DAlexis/caustic-lasertag-system/schematic/bridge/bridge-iron-rev1/bridge-iron-rev1.kicad_pcb

## KiCad design schematic/bridge/bridge-iron-rev1/bridge-iron-rev1.kicad_pcb (2015-09-06)

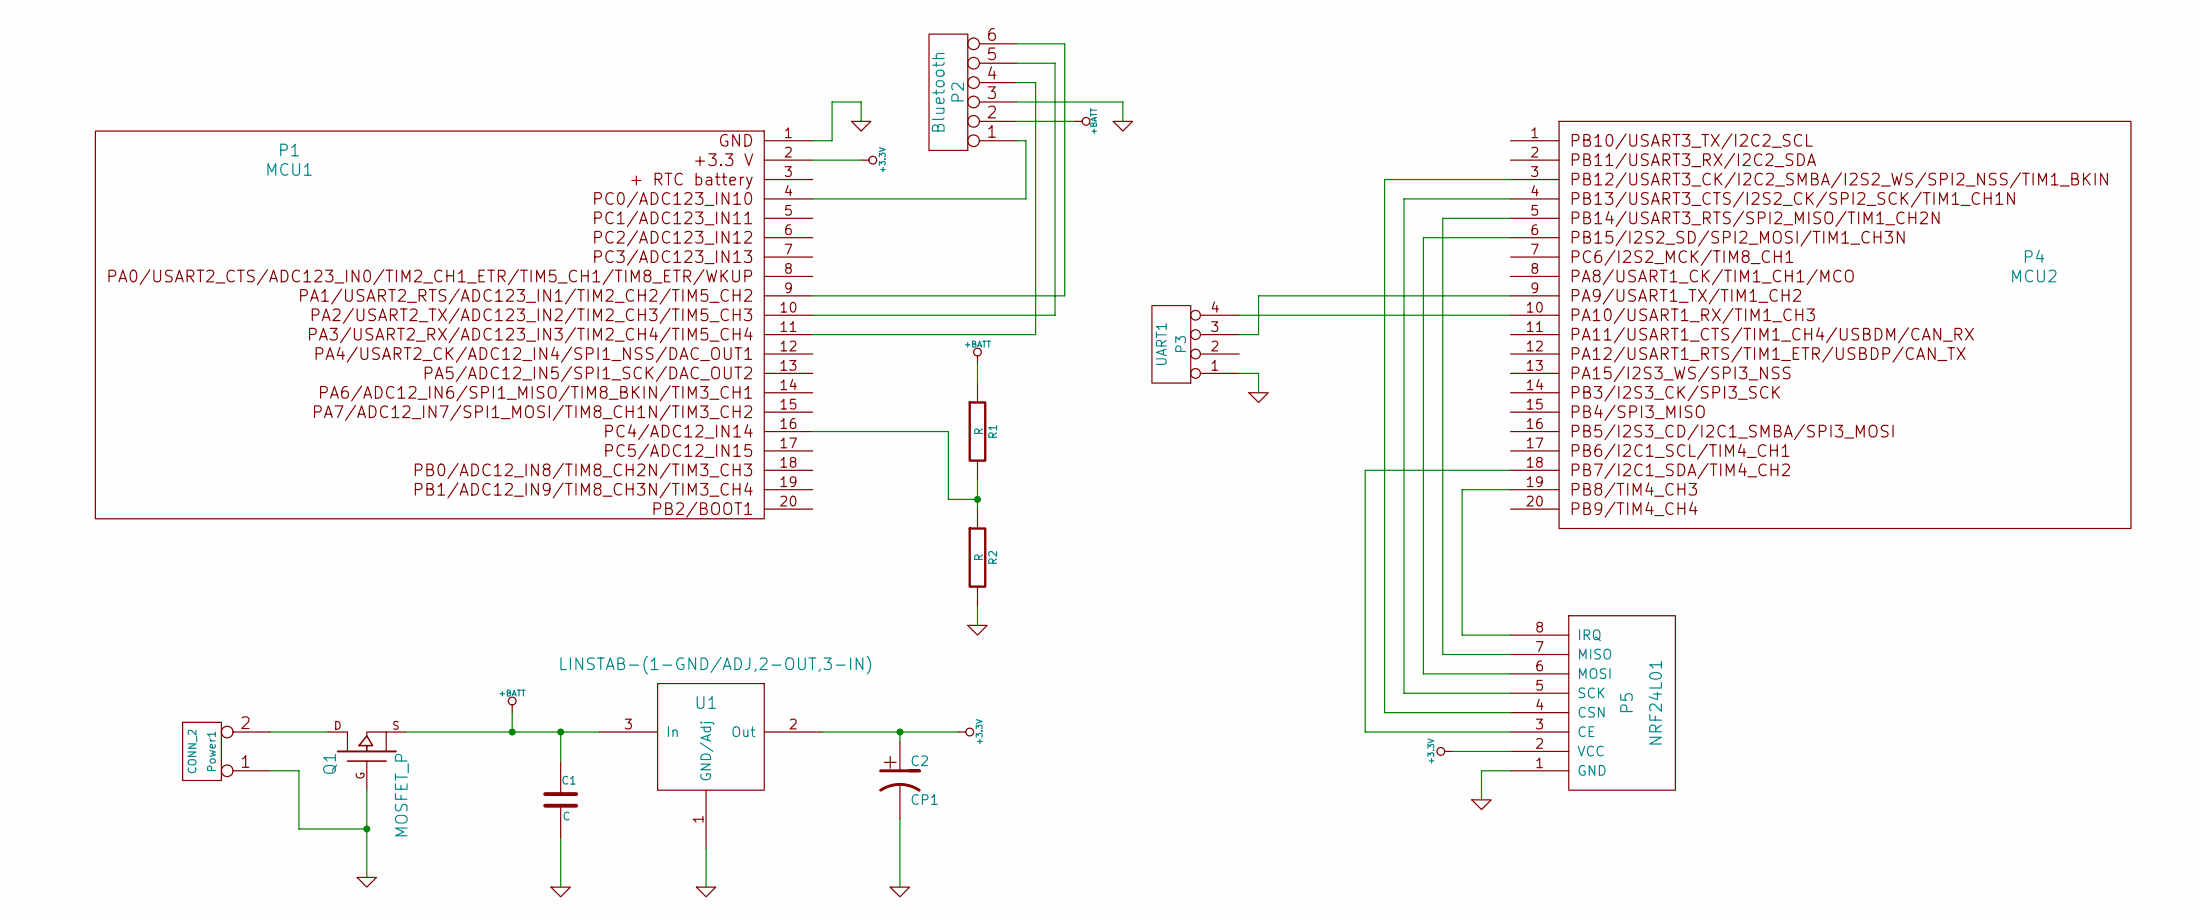
[picture p26: schematic bridge-iron-rev1.sch]

Parts:
C1: C
C2: CP1
P1: MCU1
P2: Bluetooth
P3: UART1
P4: MCU2
P5: NRF24L01
Power1: CONN_2
Q1: MOSFET_P
R1, R2: R
U1: LINSTAB-(1-GND/ADJ,2-OUT,3-IN)

Connections:
+3.3V: C2.1, P1.2, P5.2 (VCC), U1.2 (Out)
+BATT: C1.1, P2.2, Q1.S, R1.1, U1.3 (In)
GND: C1.2, C2.2, P1.1, P2.3, P3.1, P5.1 (GND), Power1.1, Q1.G, R2.2, U1.1 (GND/Adj)
unnamed: P4.18, P5.3 (CE)
unnamed: P3.3, P4.9
unnamed: P3.4, P4.10
unnamed: P4.4, P5.5 (SCK)
unnamed: P4.6, P5.6 (MOSI)
unnamed: P4.5, P5.7 (MISO)
unnamed: P4.19, P5.8 (IRQ)
unnamed: P4.3, P5.4 (CSN)
unnamed: P1.9, P2.6
unnamed: P1.4, P2.1
unnamed: Power1.2 (PM), Q1.D
unnamed: P1.11, P2.4
unnamed: P1.10, P2.5
unnamed: P1.16, R1.2, R2.1

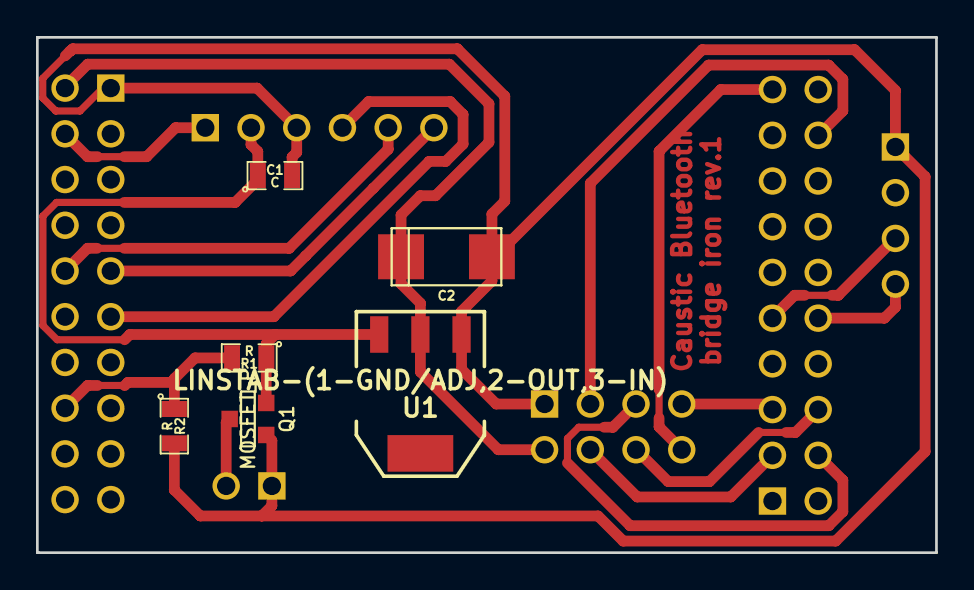
[picture p27: board bridge-iron-rev1.kicad_pcb from above]

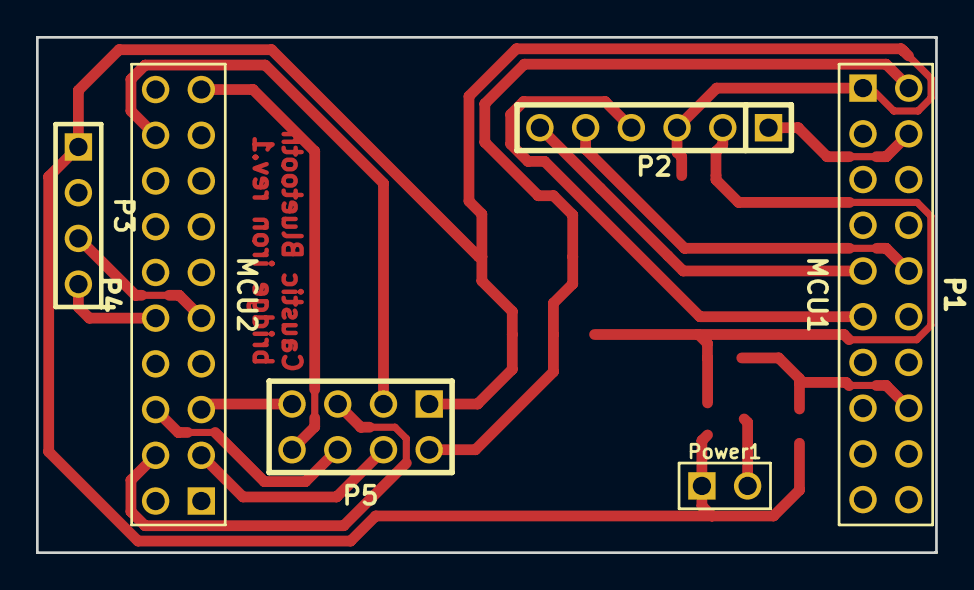
[picture p28: board bridge-iron-rev1.kicad_pcb from below]

Board: 2 copper layers, 50.0 x 28.6 mm, 12 parts (6 on the bottom side), 17 nets.
