DAlexis/caustic-lasertag-system/schematic/head-sensor/head-sensor-shield-v1-rev1/head-sensor-shield-v1-rev1.kicad_pcb

## KiCad design schematic/head-sensor/head-sensor-shield-v1-rev1/head-sensor-shield-v1-rev1.kicad_pcb (2015-08-30, an earlier design)

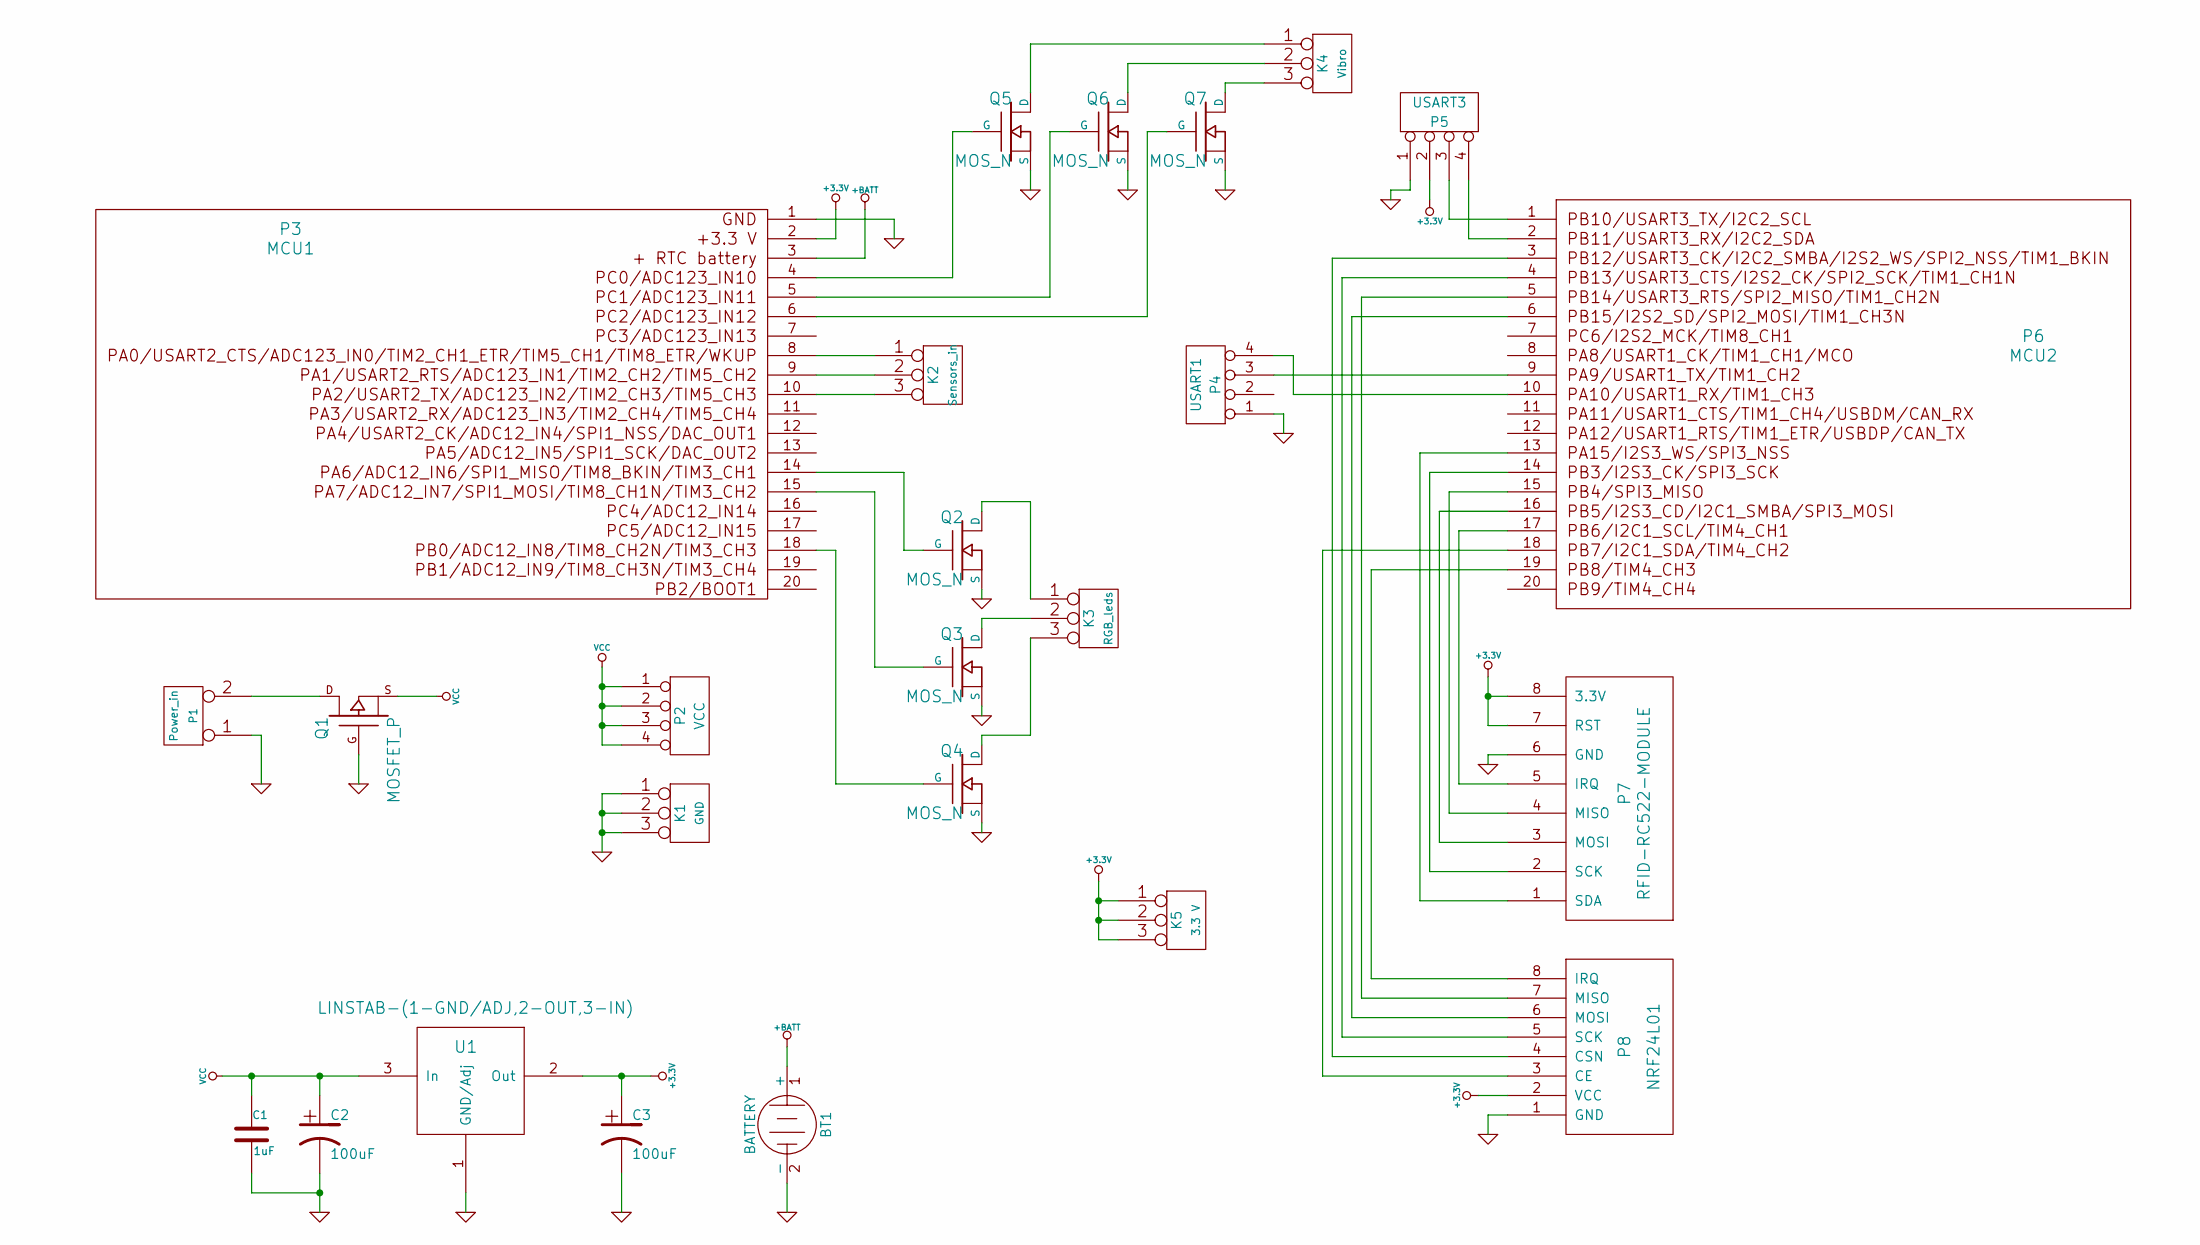
[picture p29: schematic head-sensor-shield-v1-rev1.sch]

Parts:
BT1: BATTERY
C1: 1uF
C2, C3: 100uF
K1: GND
K2: Sensors_in
K3: RGB_leds
K4: Vibro
K5: 3.3 V
P1: Power_in
P2: VCC
P3: MCU1
P4: USART1
P5: USART3
P6: MCU2
P7: RFID-RC522-MODULE
P8: NRF24L01
Q1: MOSFET_P
Q2, Q3, Q4, Q5, Q6, Q7: MOS_N
U1: LINSTAB-(1-GND/ADJ,2-OUT,3-IN)

Connections:
+3.3V: C3.1, K5.1, K5.2 (PM), K5.3, P3.2, P5.2, P7.7 (RST), P7.8 (3.3V), P8.2 (VCC), U1.2 (Out)
+BATT: BT1.1 (+), P3.3
GND: BT1.2 (-), C1.2, C2.2, C3.2, K1.1, K1.2 (PM), K1.3, P1.1, P3.1, P4.1, P5.1, P7.6 (GND), P8.1 (GND), Q1.G, Q2.S, Q3.S, Q4.S, Q5.S, Q6.S, Q7.S, U1.1 (GND/Adj)
unnamed: P3.6, Q7.G
unnamed: K4.2 (PM), Q6.D
unnamed: K4.3, Q7.D
unnamed: K4.1, Q5.D
unnamed: P3.5, Q6.G
unnamed: P3.4, Q5.G
unnamed: P3.18, Q4.G
unnamed: P3.15, Q3.G
unnamed: K2.1, P3.8
unnamed: K2.3, P3.10
unnamed: K2.2 (PM), P3.9
unnamed: P5.4, P6.2
unnamed: P5.3, P6.1
unnamed: P1.2 (PM), Q1.D
unnamed: P3.14, Q2.G
unnamed: K3.2 (PM), Q3.D
unnamed: K3.3, Q4.D
unnamed: K3.1, Q2.D
unnamed: P6.17, P7.5 (IRQ)
unnamed: P6.13, P7.1 (SDA)
unnamed: P6.14, P7.2 (SCK)
unnamed: P6.16, P7.3 (MOSI)
unnamed: P6.15, P7.4 (MISO)
unnamed: P6.19, P8.8 (IRQ)
unnamed: P6.18, P8.3 (CE)
unnamed: P6.6, P8.6 (MOSI)
unnamed: P6.5, P8.7 (MISO)
unnamed: P6.4, P8.5 (SCK)
unnamed: P6.3, P8.4 (CSN)
unnamed: P4.3, P6.9
unnamed: P4.4, P6.10
VCC: C1.1, C2.1, P2.1, P2.2, P2.3, P2.4, Q1.S, U1.3 (In)

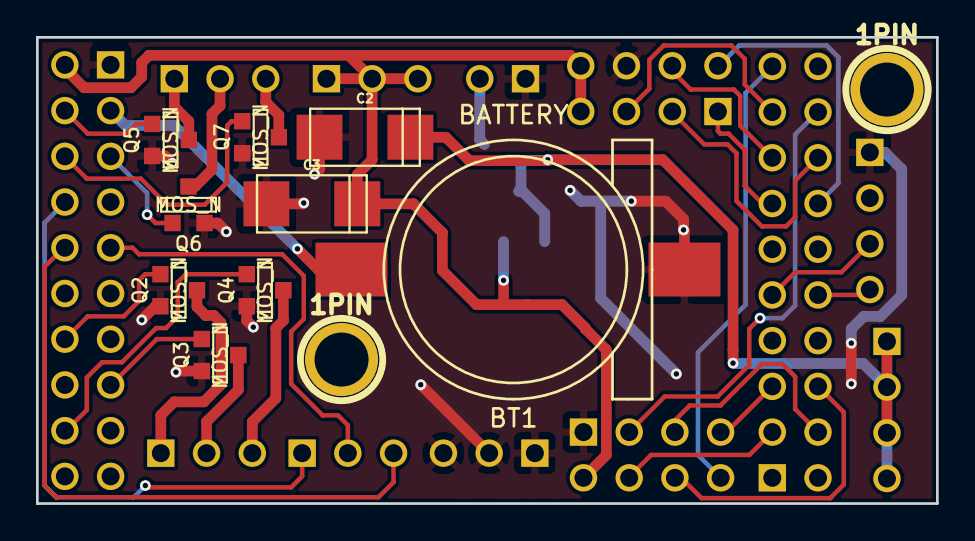
[picture p30: board head-sensor-shield-v1-rev1.kicad_pcb from above]

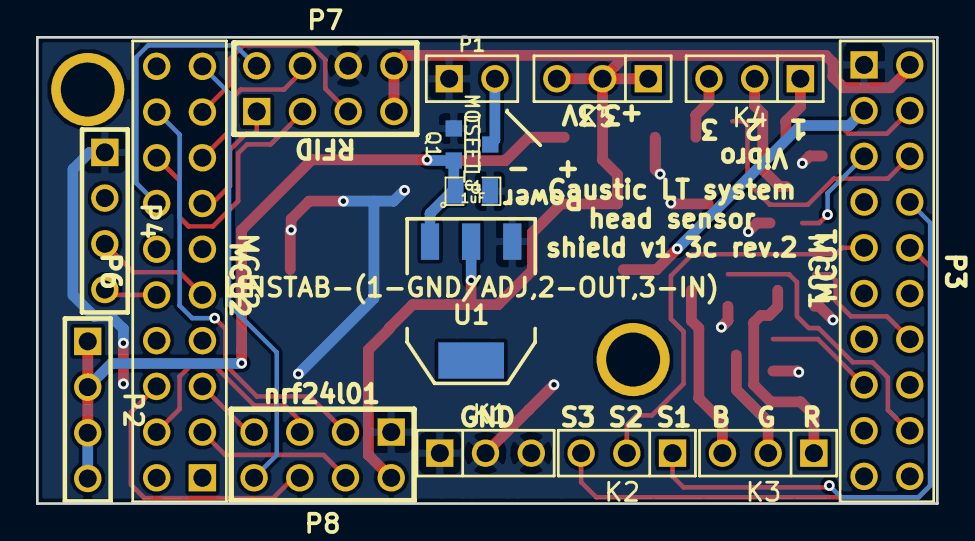
[picture p31: board head-sensor-shield-v1-rev1.kicad_pcb from below]

Board: 2 copper layers, 50.0 x 25.9 mm, 26 parts (15 on the bottom side), 33 nets.

Other parts of the board:
1PIN, 1PIN#2: P***; 1pin
