DAlexis/caustic-lasertag-system/schematic/rifle/rifle-shield-v1-rev1/rifle-shield-v1.kicad_pcb

## KiCad design schematic/rifle/rifle-shield-v1-rev1/rifle-shield-v1.kicad_pcb (2015-07-31)

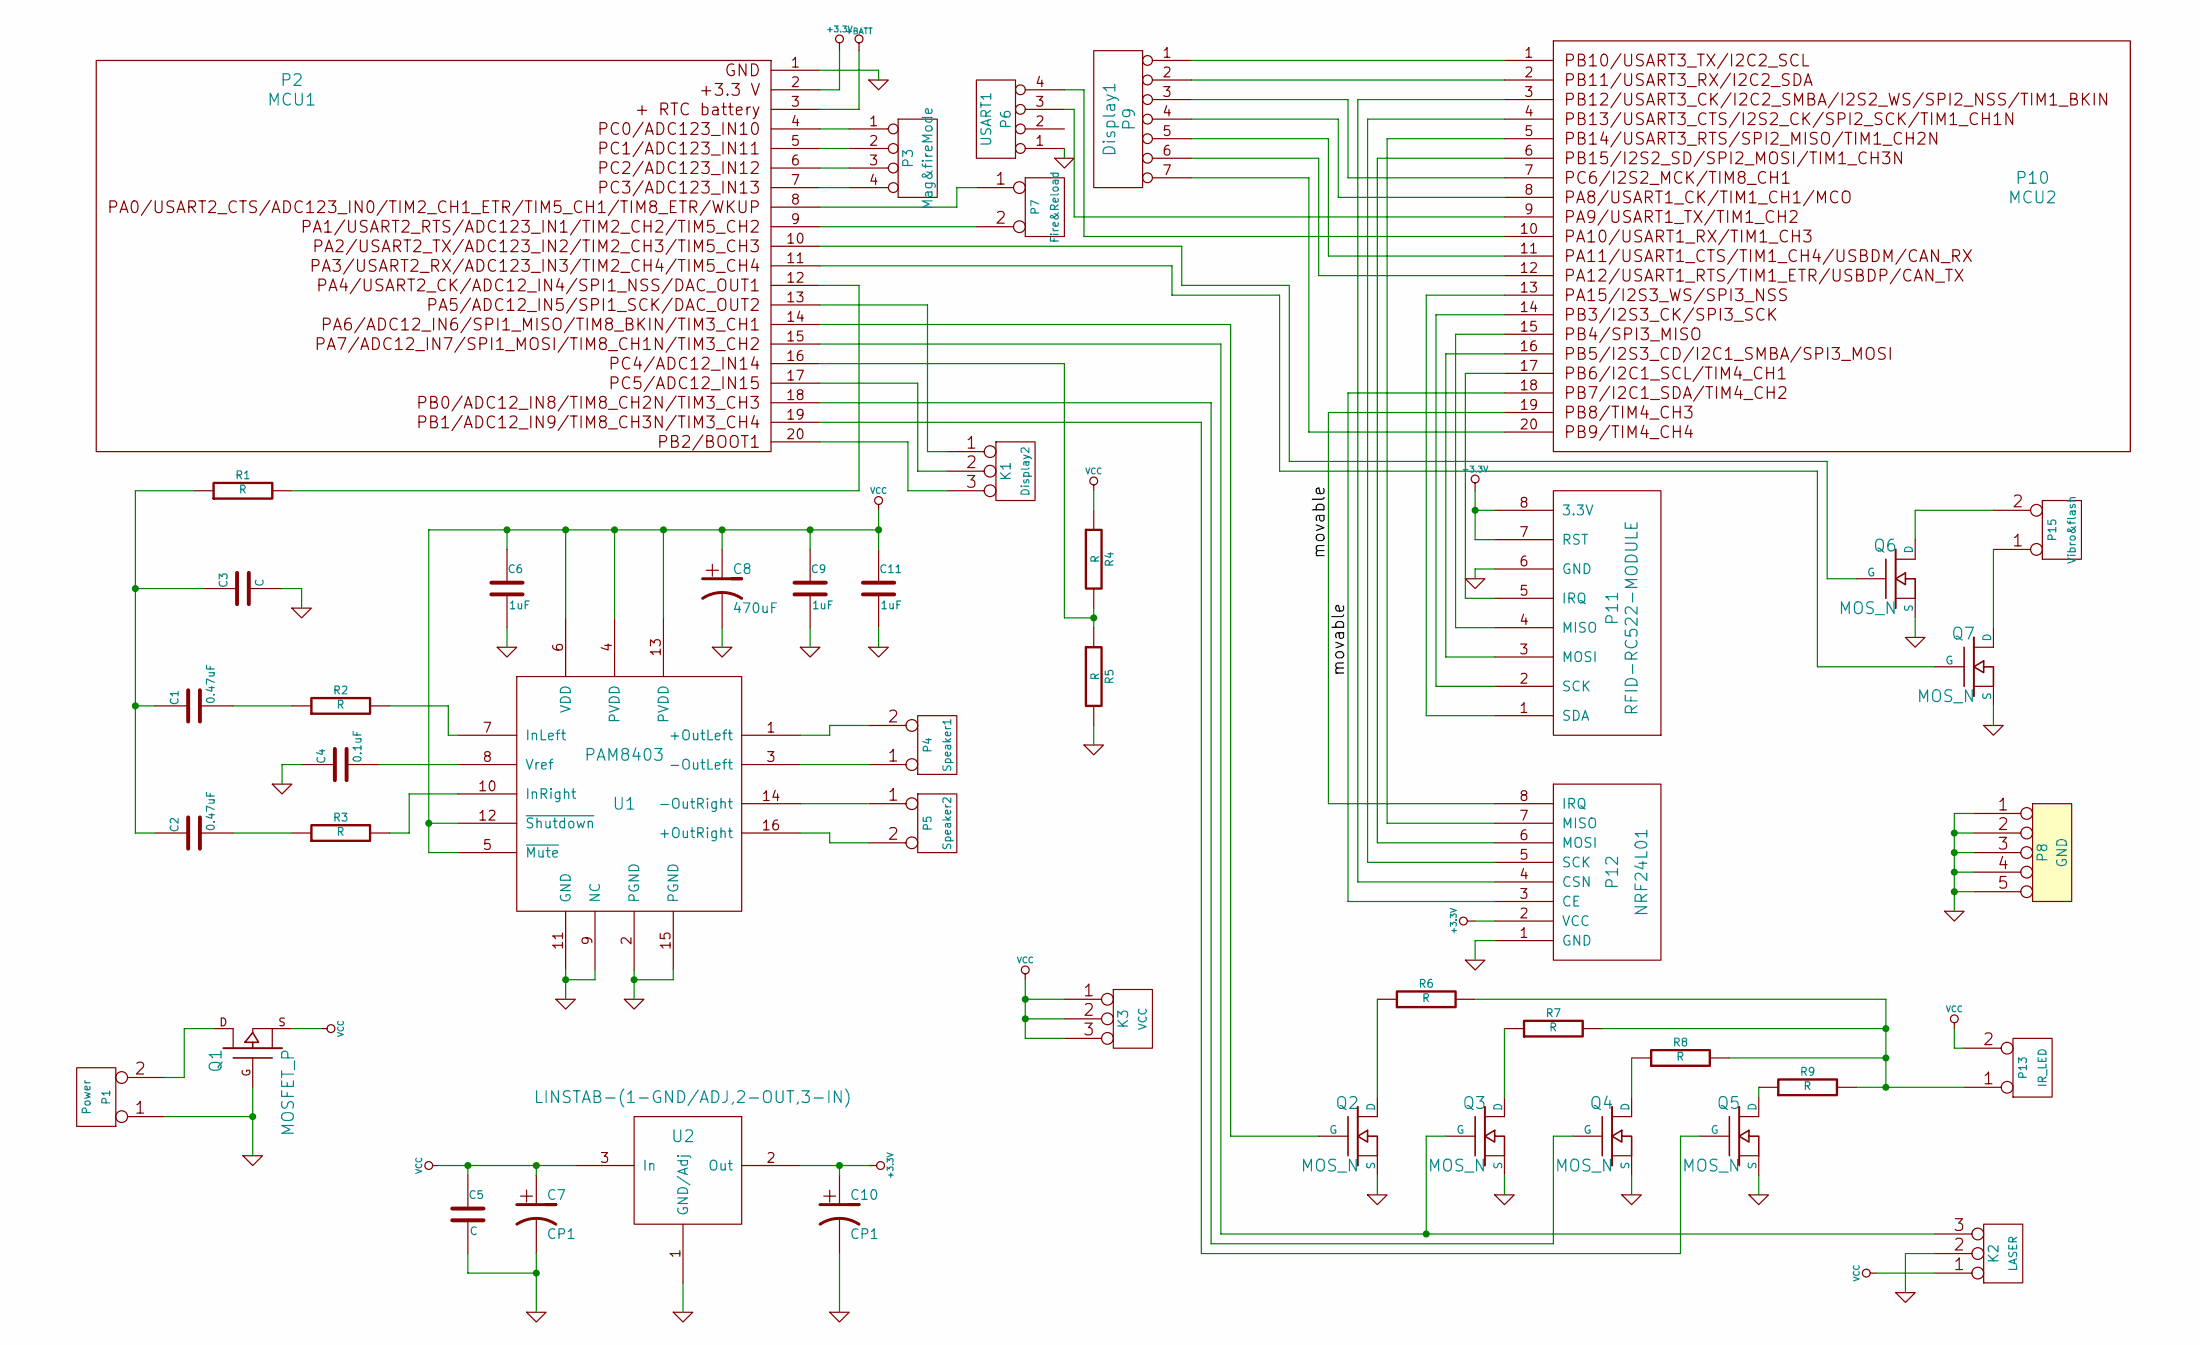
[picture p32: schematic rifle-shield-v1.sch]

Parts:
C1, C2: 0.47uF
C3, C5: C
C4: 0.1uF
C6, C9, C11: 1uF
C7, C10: CP1
C8: 470uF
K1: Display2
K2: LASER
K3: VCC
P1: Power
P2: MCU1
P3: Mag&fireMode
P4: Speaker1
P5: Speaker2
P6: USART1
P7: Fire&Reload
P8: GND
P9: Display1
P10: MCU2
P11: RFID-RC522-MODULE
P12: NRF24L01
P13: IR_LED
P15: Vibro&flash
Q1: MOSFET_P
Q2, Q3, Q4, Q5, Q6, Q7: MOS_N
R1, R2, R3, R4, R5, R6, R7, R8, R9: R
U1: PAM8403
U2: LINSTAB-(1-GND/ADJ,2-OUT,3-IN)

Connections:
+3.3V: C10.1, P2.2, P11.7 (RST), P11.8 (3.3V), P12.2 (VCC), U2.2 (Out)
/movable: P10.18, P10.19, P12.3 (CE), P12.8 (IRQ)
GND: C3.2, C4.1, C5.2, C6.2, C7.2, C8.2, C9.2, C10.2, C11.2, K2.2 (PM), P1.1, P2.1, P6.1, P8.1, P8.2, P8.3, P8.4, P8.5, P11.6 (GND), P12.1 (GND), Q1.G, Q2.S, Q3.S, Q4.S, Q5.S, Q6.S, Q7.S, R5.2, U1.2 (PGND), U1.9 (NC), U1.11 (GND), U1.15 (PGND), U2.1 (GND/Adj)
unnamed: R3.2, U1.10 (InRight)
unnamed: R2.2, U1.7 (InLeft)
unnamed: C1.2, R2.1
unnamed: C2.2, R3.1
unnamed: P2.9, P7.2 (PM)
unnamed: Q4.D, R8.1
unnamed: Q3.D, R7.1
unnamed: Q2.D, R6.1
unnamed: P2.12, R1.2
unnamed: C1.1, C2.1, C3.1, R1.1
unnamed: P2.8, P7.1
unnamed: C4.2, U1.8 (Vref)
unnamed: P2.7, P3.4
unnamed: P2.6, P3.3
unnamed: P2.5, P3.2
unnamed: P2.4, P3.1
unnamed: P5.2 (PM), U1.16 (+OutRight)
unnamed: P5.1, U1.14 (-OutRight)
unnamed: P4.2 (PM), U1.1 (+OutLeft)
unnamed: P4.1, U1.3 (-OutLeft)
unnamed: P10.17, P11.5 (IRQ)
unnamed: P10.3, P12.4 (CSN)
unnamed: P10.4, P12.5 (SCK)
unnamed: P10.6, P12.6 (MOSI)
unnamed: P10.5, P12.7 (MISO)
unnamed: P10.13, P11.1 (SDA)
unnamed: P10.14, P11.2 (SCK)
unnamed: P10.16, P11.3 (MOSI)
unnamed: P10.15, P11.4 (MISO)
unnamed: Q5.D, R9.1
unnamed: P9.5, P10.11
unnamed: K1.1, P2.13
unnamed: P9.7, P10.20
unnamed: P9.6, P10.12
unnamed: P6.4, P10.10
unnamed: P6.3, P10.9
unnamed: P9.4, P10.8
unnamed: P9.3, P10.7
unnamed: P9.2, P10.2
unnamed: P9.1, P10.1
unnamed: P2.16, R4.2, R5.1
unnamed: K1.3, P2.20
unnamed: K1.2 (PM), P2.17
unnamed: P2.19, Q5.G
unnamed: P2.18, Q4.G
unnamed: K2.3, P2.15, Q3.G
unnamed: P2.14, Q2.G
unnamed: P13.1, R6.2, R7.2, R8.2, R9.2
unnamed: P2.11, Q7.G
unnamed: P2.10, Q6.G
unnamed: P15.1, Q7.D
unnamed: P15.2 (PM), Q6.D
unnamed: P1.2 (PM), Q1.D
VCC: C5.1, C6.1, C7.1, C8.1, C9.1, C11.1, K2.1, K3.1, K3.2 (PM), K3.3, P13.2 (PM), Q1.S, R4.1, U1.4 (PVDD), U1.5 (~Mute), U1.6 (VDD), U1.12 (~Shutdown), U1.13 (PVDD), U2.3 (In)

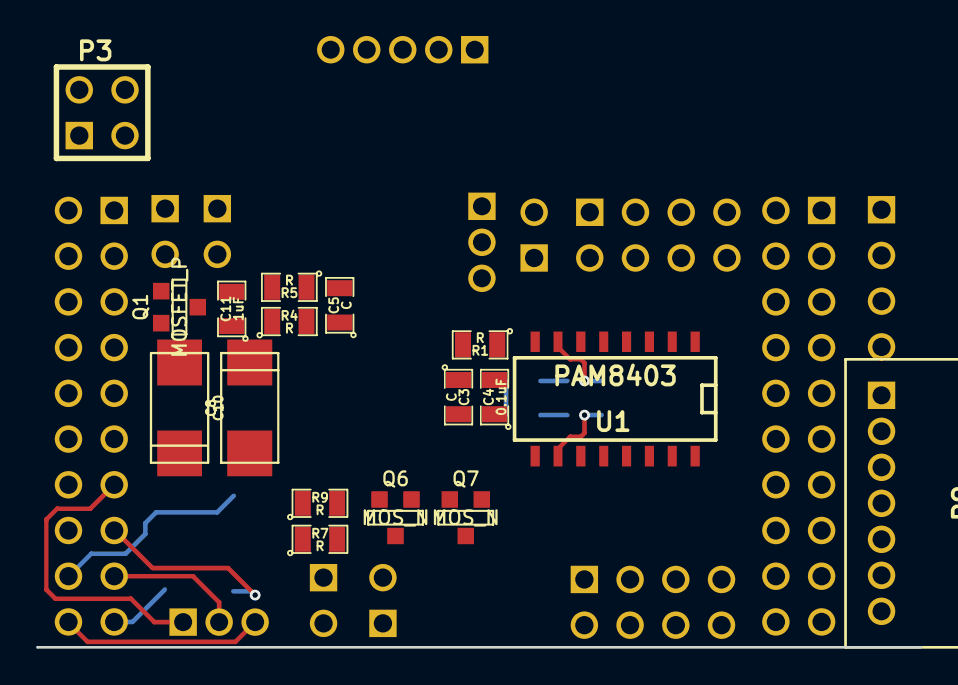
[picture p33: board rifle-shield-v1.kicad_pcb from above]

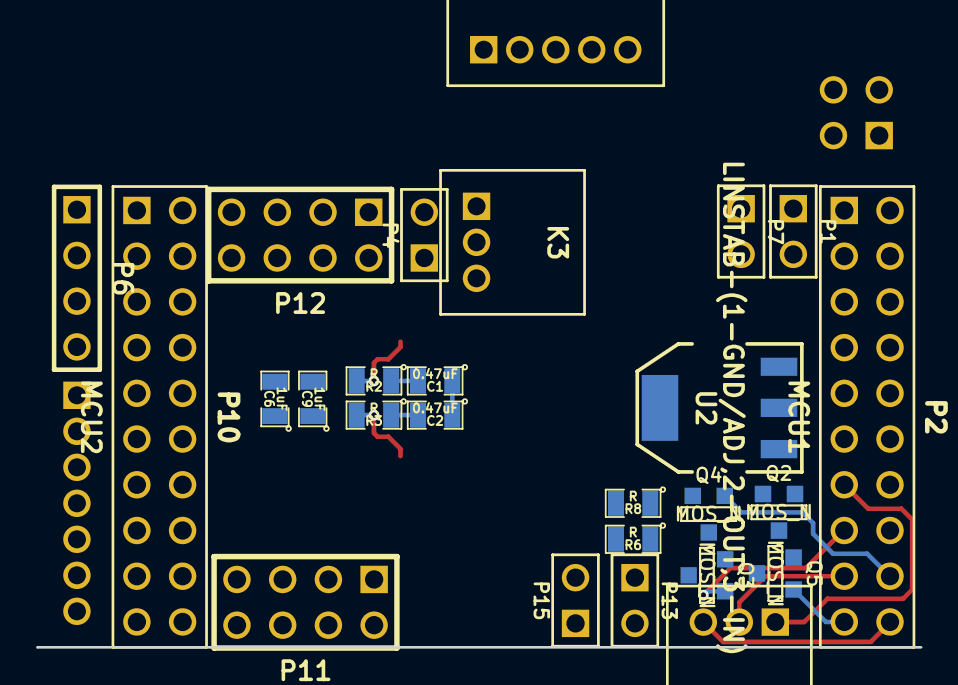
[picture p34: board rifle-shield-v1.kicad_pcb from below]

Board: 2 copper layers, 43 parts (26 on the bottom side), 55 nets.
