DAlexis/caustic-lasertag-system/schematic/sensor-module/sensor-module-rev1-lit/sensor-module.kicad_pcb

## KiCad design schematic/sensor-module/sensor-module-rev1-lit/sensor-module.kicad_pcb (2015-04-21, an earlier design)

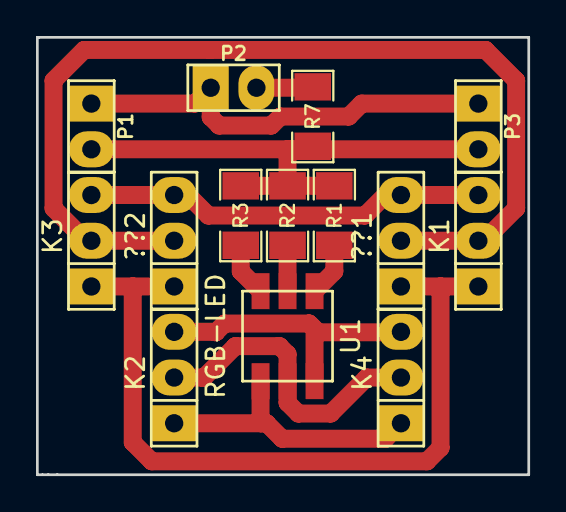
[picture p35: board schematic/sensor-module/sensor-module-rev1-lit/sensor-module.kicad_pcb from above]

Board: 2 copper layers, 27.3 x 24.3 mm, 14 parts (0 on the bottom side), 12 nets.

Parts:
??1, ??2: TSOP4856; PIN_ARRAY_LARGE_PADS_2.54mm_3X1
K1, K3: SENSORS; PIN_ARRAY_LARGE_PADS_2.54mm_3X1
K2, K4: LEDs; PIN_ARRAY_LARGE_PADS_2.54mm_3X1
P1, P3: Vibro; PIN_ARRAY_LARGE_PADS_2.54mm_2X1
P2: VibroEngine; PIN_ARRAY_LARGE_PADS_2.54mm_2X1
R1, R2, R3, R7: R; SM1206
U1: RGB-LED; RGB-led

Connections:
+3.3V: ??1.3, ??2.3, K1.3, K3.3
+BATT: P1.2, P3.2, R1.1, R2.1, R3.1, R7.2
GND: ??1.2, ??2.2, K1.2, K3.2
unnamed: K2.1, K4.1, U1.1
unnamed: R1.2, U1.4
unnamed: R2.2, U1.5
unnamed: R3.2, U1.6
unnamed: K2.2, K4.2, U1.2
unnamed: ??1.1, ??2.1, K1.1, K3.1
unnamed: P2.2, R7.1
unnamed: P1.1, P2.1, P3.1
unnamed: K2.3, K4.3, U1.3
