DAlexis/caustic-lasertag-system/schematic/simple-ir-remote-control/simple-ir-remote-control-rev1.1/simple-ir-remote-control.kicad_pcb

## KiCad design schematic/simple-ir-remote-control/simple-ir-remote-control-rev1.1/simple-ir-remote-control.kicad_pcb (2015-02-28)

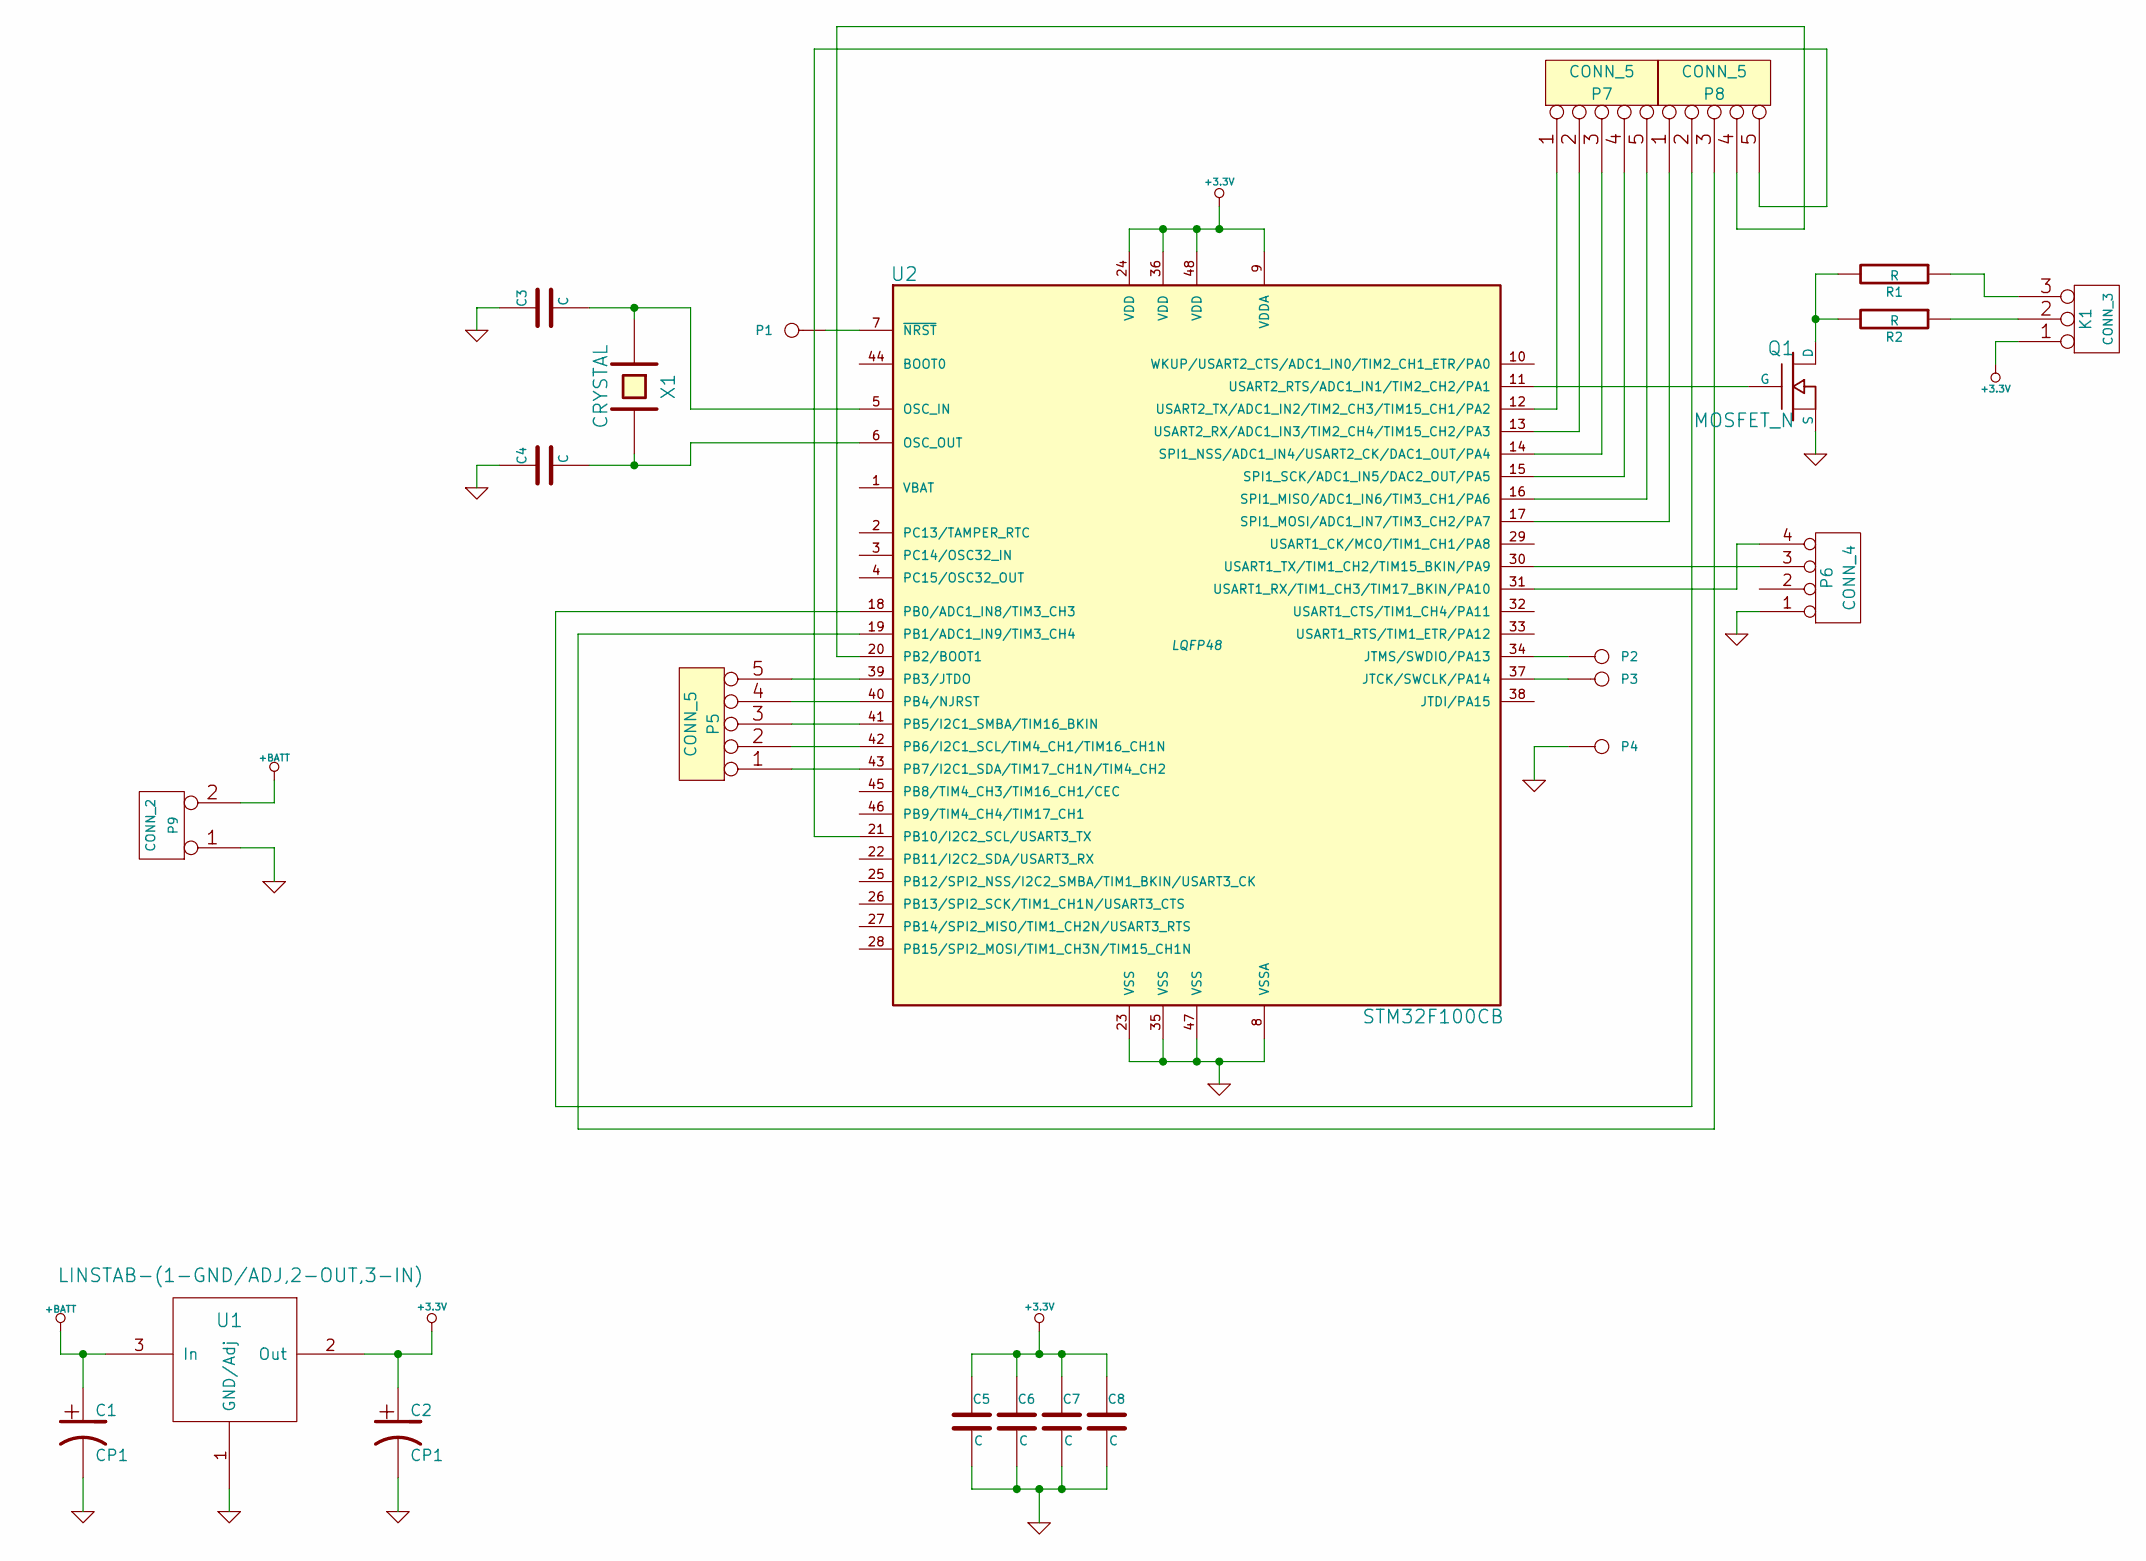
[picture p36: schematic simple-ir-remote-control.sch]

Parts:
C1, C2: CP1
C3, C4, C5, C6, C7, C8: C
K1: CONN_3
P1, P2, P3, P4: CONN_1
P5, P7, P8: CONN_5
P6: CONN_4
P9: CONN_2
Q1: MOSFET_N
R1, R2: R
U1: LINSTAB-(1-GND/ADJ,2-OUT,3-IN)
U2: STM32F100CB; LQFP48
X1: CRYSTAL

Connections:
+3.3V: C2.1, C5.1, C6.1, C7.1, C8.1, K1.1, U1.2 (Out), U2.9 (VDDA), U2.24 (VDD), U2.36 (VDD), U2.48 (VDD)
+BATT: C1.1, P9.2 (PM), U1.3 (In)
GND: C1.2, C2.2, C3.1, C4.1, C5.2, C6.2, C7.2, C8.2, P4.1, P6.1, P9.1, Q1.S, U1.1 (GND/Adj), U2.8 (VSSA), U2.23 (VSS), U2.35 (VSS), U2.47 (VSS); also elsewhere on the board
unnamed: Q1.D, R1.2, R2.2
unnamed: K1.2 (PM), R2.1
unnamed: K1.3, R1.1
unnamed: Q1.G, U2.11 (USART2_RTS/ADC1_IN1/TIM2_CH2/PA1)
unnamed: P6.4, U2.31 (USART1_RX/TIM1_CH3/TIM17_BKIN/PA10)
unnamed: P5.3, U2.41 (PB5/I2C1_SMBA/TIM16_BKIN)
unnamed: P5.4, U2.40 (PB4/NJRST)
unnamed: P5.5, U2.39 (PB3/JTDO)
unnamed: P6.3, U2.30 (USART1_TX/TIM1_CH2/TIM15_BKIN/PA9)
unnamed: P5.2, U2.42 (PB6/I2C1_SCL/TIM4_CH1/TIM16_CH1N)
unnamed: P1.1, U2.7 (~NRST)
unnamed: P2.1, U2.34 (JTMS/SWDIO/PA13)
unnamed: P3.1, U2.37 (JTCK/SWCLK/PA14)
unnamed: P8.3, U2.19 (PB1/ADC1_IN9/TIM3_CH4)
unnamed: P8.5, U2.21 (PB10/I2C2_SCL/USART3_TX)
unnamed: P8.2, U2.18 (PB0/ADC1_IN8/TIM3_CH3)
unnamed: P8.1, U2.17 (SPI1_MOSI/ADC1_IN7/TIM3_CH2/PA7)
unnamed: P7.5, U2.16 (SPI1_MISO/ADC1_IN6/TIM3_CH1/PA6)
unnamed: P7.4, U2.15 (SPI1_SCK/ADC1_IN5/DAC2_OUT/PA5)
unnamed: P7.3, U2.14 (SPI1_NSS/ADC1_IN4/USART2_CK/DAC1_OUT/PA4)
unnamed: P7.1, U2.12 (USART2_TX/ADC1_IN2/TIM2_CH3/TIM15_CH1/P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)
unnamed: P7.2, U2.13 (USART2_RX/ADC1_IN3/TIM2_CH4/TIM15_CH2/P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)
unnamed: P5.1, U2.43 (PB7/I2C1_SDA/TIM17_CH1N/TIM4_CH2)
unnamed: P8.4, U2.20 (PB2/BOOT1)
unnamed: C4.2, U2.6 (OSC_OUT), X1.2
unnamed: C3.2, U2.5 (OSC_IN), X1.1

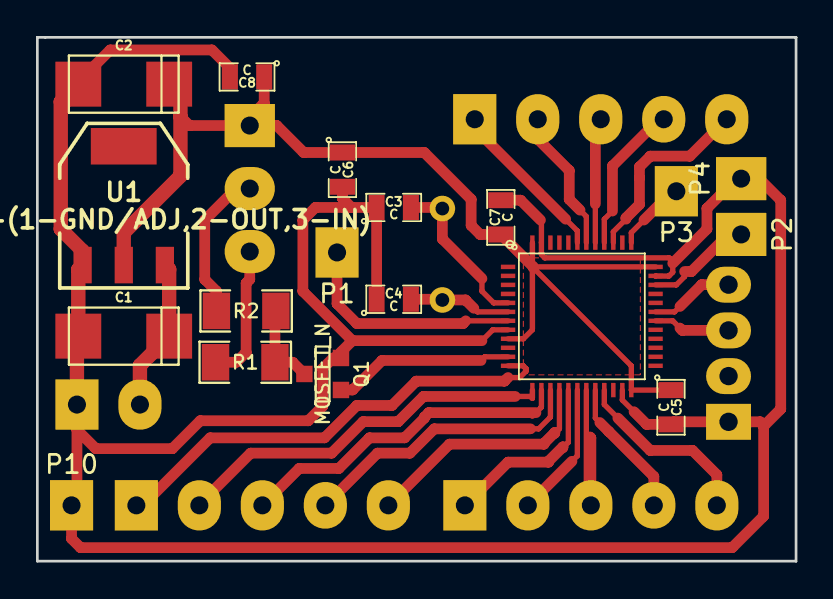
[picture p37: board simple-ir-remote-control.kicad_pcb from above]

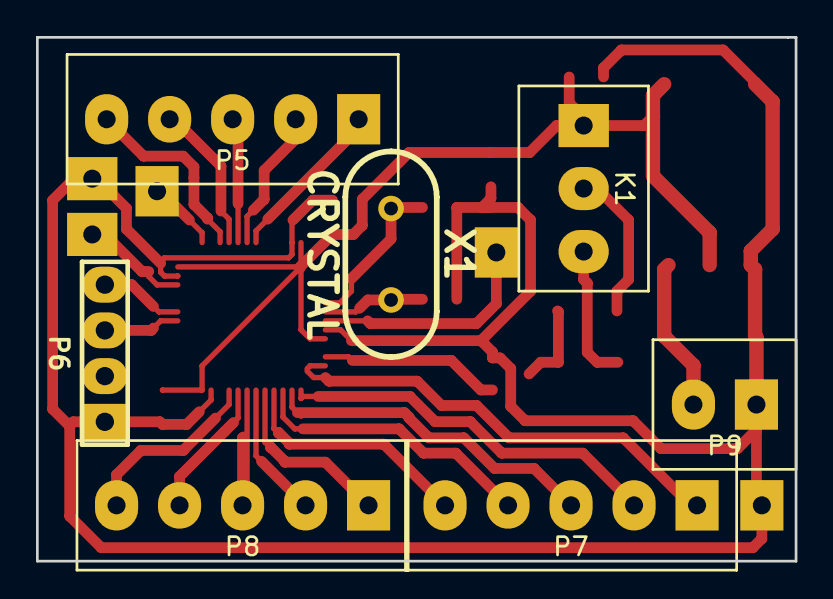
[picture p38: board simple-ir-remote-control.kicad_pcb from below]

Board: 2 copper layers, 42.2 x 29.1 mm, 25 parts (7 on the bottom side), 29 nets.

Other parts of the board:
P10: CONN_1; PIN_ARRAY_LARGE_PADS_3.5mm_1

Their connections:
GND: P10.1; also elsewhere on the board
