DAlexis/caustic-lasertag-system/schematic/rifle/rifle-stm32f103ret6-rev1.1/rifle.kicad_pcb

## KiCad design schematic/rifle/rifle-stm32f103ret6-rev1.1/rifle.kicad_pcb (2015-02-20)

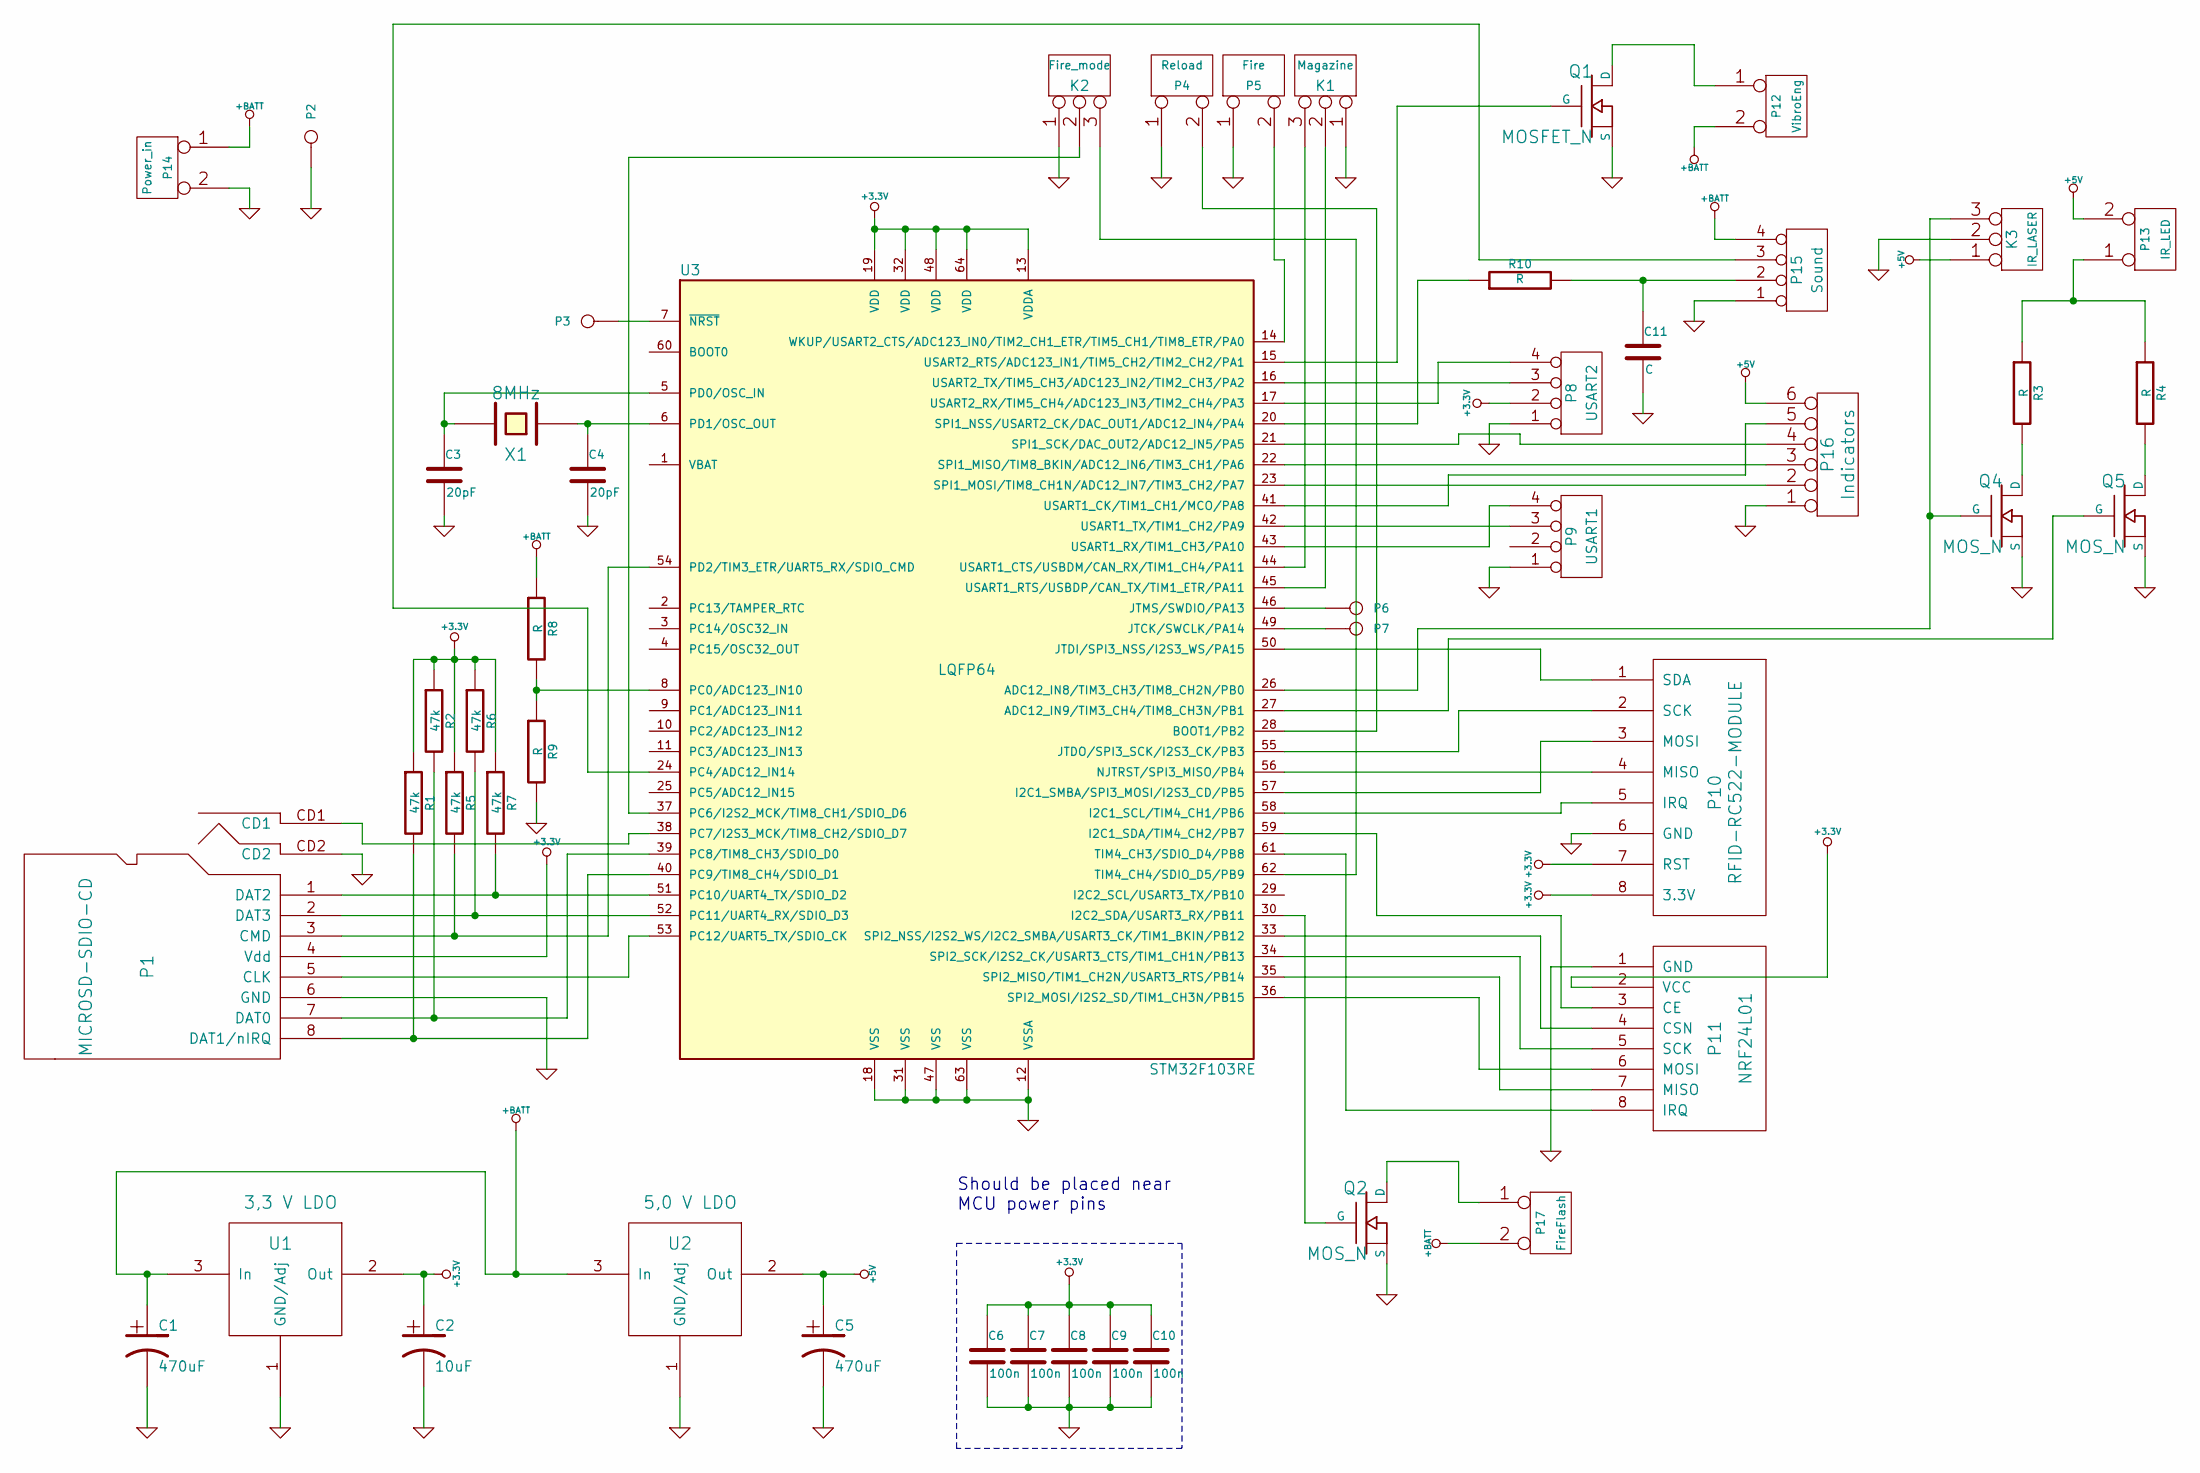
[picture p39: schematic rifle.sch]

Parts:
C1, C5: 470uF
C2: 10uF
C3, C4: 20pF
C6, C7, C8, C9, C10: 100n
C11: C
K1: Magazine
K2: Fire_mode
K3: IR_LASER
P1: MICROSD-SDIO-CD
P2: GND
P3: Reset
P4: Reload
P5: Fire
P6: SWD_IO
P7: SWD_CLK
P8: USART2
P9: USART1
P10: RFID-RC522-MODULE
P11: NRF24L01
P12: VibroEng
P13: IR_LED
P14: Power_in
P15: Sound
P16: Indicators
P17: FireFlash
Q1: MOSFET_N
Q2, Q4, Q5: MOS_N
R1, R2, R5, R6, R7: 47k
R3, R4, R8, R9, R10: R
U1: 3,3 V LDO
U2: 5,0 V LDO
U3: STM32F103RE; LQFP64
X1: 8MHz

Connections:
+3.3V: C2.1, C6.1, C7.1, C8.1, C9.1, C10.1, P1.4 (Vdd), P8.2, P10.7 (RST), P10.8 (3.3V), P11.2 (VCC), R1.1, R2.1, R5.1, R6.1, R7.1, U1.2 (Out), U3.13 (VDDA), U3.19 (VDD), U3.32 (VDD), U3.48 (VDD), U3.64 (VDD)
+5V: C5.1, K3.1, P13.2 (PM), P16.6, U2.2 (Out)
+BATT: C1.1, P12.2 (PM), P14.1, P15.4, P17.2 (PM), R8.1, U1.3 (In), U2.3 (In)
GND: C1.2, C2.2, C3.2, C4.2, C5.2, C6.2, C7.2, C8.2, C9.2, C10.2, C11.2, K1.1, K2.1, K3.2 (PM), P1.6 (GND), P1.CD2, P2.1, P4.1, P5.1, P8.1, P9.1, P10.6 (GND), P11.1 (GND), P14.2 (PM), P15.1, P16.1, Q1.S, Q2.S, Q4.S, Q5.S, R9.2, U1.1 (GND/Adj), U2.1 (GND/Adj), U3.12 (VSSA), U3.18 (VSS), U3.31 (VSS), U3.47 (VSS), U3.63 (VSS)
unnamed: Q4.D, R3.2
unnamed: Q5.D, R4.2
unnamed: K3.3, Q4.G, U3.26 (ADC12_IN8/TIM3_CH3/TIM8_CH2N/PB0)
unnamed: Q5.G, U3.27 (ADC12_IN9/TIM3_CH4/TIM8_CH3N/PB1)
unnamed: P11.4 (CSN), U3.33 (SPI2_NSS/I2S2_WS/I2C2_SMBA/USART3_CK/TI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)
unnamed: P11.6 (MOSI), U3.36 (SPI2_MOSI/I2S2_SD/TIM1_CH3N/PB15)
unnamed: P11.7 (MISO), U3.35 (SPI2_MISO/TIM1_CH2N/USART3_RTS/PB14)
unnamed: P11.5 (SCK), U3.34 (SPI2_SCK/I2S2_CK/USART3_CTS/TIM1_CH1N/P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)
unnamed: P11.8 (IRQ), U3.61 (TIM4_CH3/SDIO_D4/PB8)
unnamed: P11.3 (CE), U3.59 (I2C1_SDA/TIM4_CH2/PB7)
unnamed: Q1.G, U3.15 (USART2_RTS/ADC123_IN1/TIM5_CH2/TIM2_CH2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)
unnamed: K1.3, U3.44 (USART1_CTS/USBDM/CAN_RX/TIM1_CH4/PA11)
unnamed: K1.2 (PM), U3.45 (USART1_RTS/USBDP/CAN_TX/TIM1_ETR/PA11)
unnamed: P1.5 (CLK), U3.53 (PC12/UART5_TX/SDIO_CK)
unnamed: C4.1, U3.6 (PD1/OSC_OUT), X1.1
unnamed: C3.1, U3.5 (PD0/OSC_IN), X1.2
unnamed: P10.1 (SDA), U3.50 (JTDI/SPI3_NSS/I2S3_WS/PA15)
unnamed: P8.4, U3.17 (USART2_RX/TIM5_CH4/ADC123_IN3/TIM2_CH4/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)
unnamed: P10.4 (MISO), U3.56 (NJTRST/SPI3_MISO/PB4)
unnamed: P10.3 (MOSI), U3.57 (I2C1_SMBA/SPI3_MOSI/I2S3_CD/PB5)
unnamed: P10.5 (IRQ), U3.58 (I2C1_SCL/TIM4_CH1/PB6)
unnamed: P3.1, U3.7 (~NRST)
unnamed: P6.1, U3.46 (JTMS/SWDIO/PA13)
unnamed: P7.1, U3.49 (JTCK/SWCLK/PA14)
unnamed: P9.3, U3.42 (USART1_TX/TIM1_CH2/PA9)
unnamed: P9.4, U3.43 (USART1_RX/TIM1_CH3/PA10)
unnamed: P8.3, U3.16 (USART2_TX/TIM5_CH3/ADC123_IN2/TIM2_CH3/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)
unnamed: P4.2 (PM), U3.28 (BOOT1/PB2)
unnamed: P5.2 (PM), U3.14 (WKUP/USART2_CTS/ADC123_IN0/TIM2_CH1_ETR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)
unnamed: P1.CD1, U3.38 (PC7/I2S3_MCK/TIM8_CH2/SDIO_D7)
unnamed: P1.2 (DAT3), R6.2, U3.52 (PC11/UART4_RX/SDIO_D3)
unnamed: P1.1 (DAT2), R7.2, U3.51 (PC10/UART4_TX/SDIO_D2)
unnamed: K2.2 (PM), U3.37 (PC6/I2S2_MCK/TIM8_CH1/SDIO_D6)
unnamed: R10.1, U3.20 (SPI1_NSS/USART2_CK/DAC_OUT1/ADC12_IN4/P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)
unnamed: P13.1, R3.1, R4.1
unnamed: P17.1, Q2.D
unnamed: Q2.G, U3.30 (I2C2_SDA/USART3_RX/PB11)
unnamed: C11.1, P15.2, R10.2
unnamed: P15.3, U3.24 (PC4/ADC12_IN14)
unnamed: P16.2, U3.23 (SPI1_MOSI/TIM8_CH1N/ADC12_IN7/TIM3_CH2/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)
unnamed: P16.3, U3.22 (SPI1_MISO/TIM8_BKIN/ADC12_IN6/TIM3_CH1/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)
unnamed: P16.4, U3.21 (SPI1_SCK/DAC_OUT2/ADC12_IN5/PA5)
unnamed: P12.1, Q1.D
unnamed: K2.3, U3.62 (TIM4_CH4/SDIO_D5/PB9)
unnamed: P10.2 (SCK), U3.55 (JTDO/SPI3_SCK/I2S3_CK/PB3)
unnamed: P1.8 (DAT1/nIRQ), R1.2, U3.40 (PC9/TIM8_CH4/SDIO_D1)
unnamed: P1.7 (DAT0), R2.2, U3.39 (PC8/TIM8_CH3/SDIO_D0)
unnamed: P1.3 (CMD), R5.2, U3.54 (PD2/TIM3_ETR/UART5_RX/SDIO_CMD)
unnamed: P16.5, U3.41 (USART1_CK/TIM1_CH1/MCO/PA8)
unnamed: R8.2, R9.1, U3.8 (PC0/ADC123_IN10)

Notes on the sheet:
Should be placed near MCU power pins

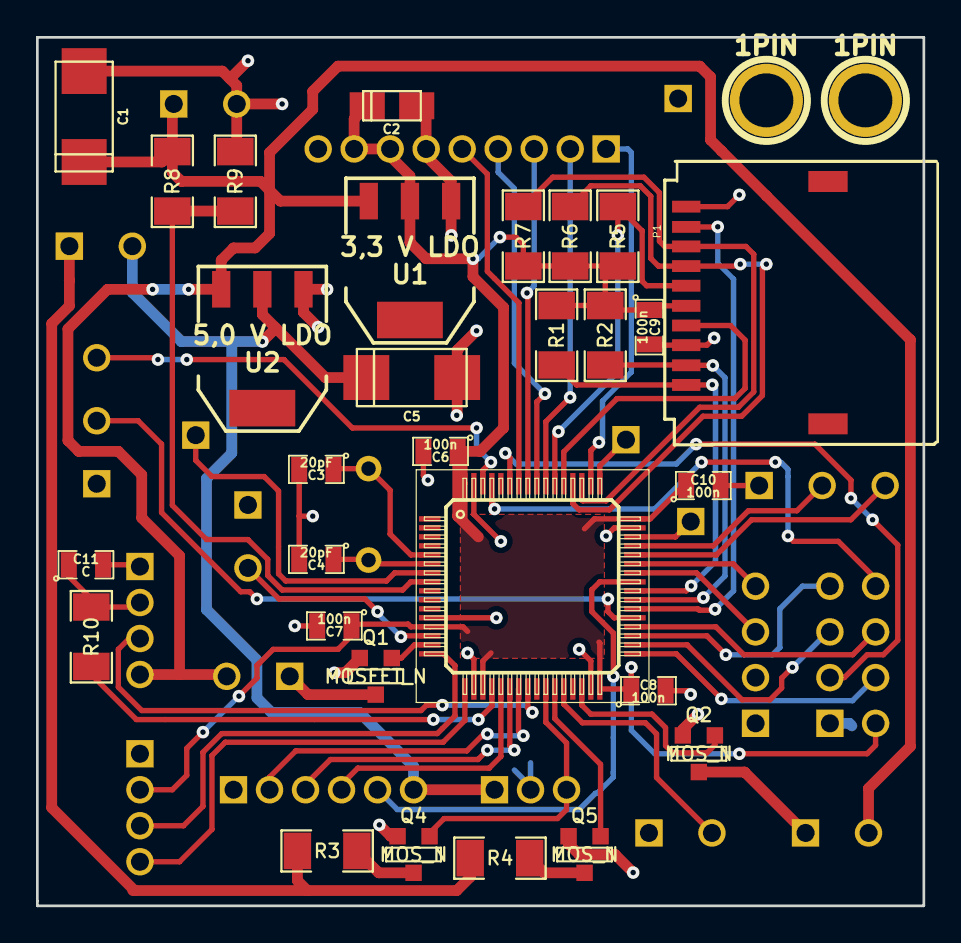
[picture p40: board rifle.kicad_pcb from above]

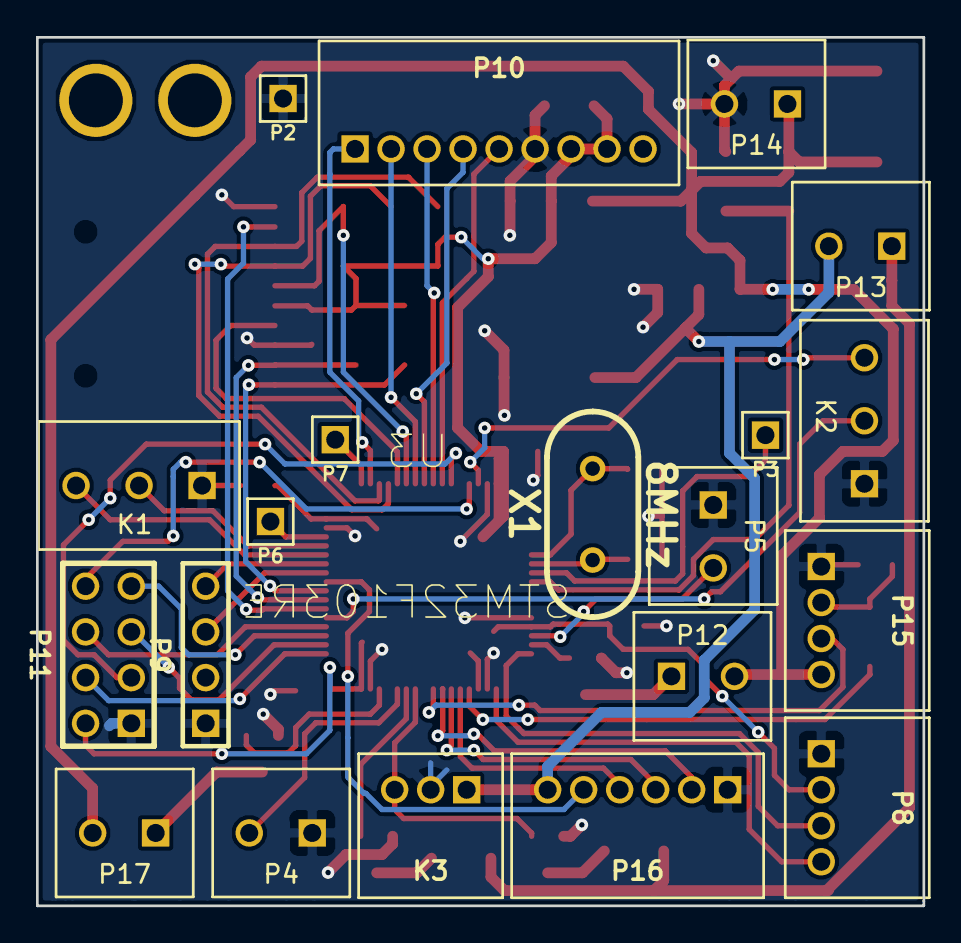
[picture p41: board rifle.kicad_pcb from below]

Board: 2 copper layers, 49.2 x 48.2 mm, 51 parts (20 on the bottom side), 54 nets.

Other parts of the board:
1PIN, 1PIN#2: P***; 1pin
