DAlexis/caustic-lasertag-system/schematic/head-sensor/head-sensor-stm32f103ret6-rev1.1/head-sensor.kicad_pcb

## KiCad design schematic/head-sensor/head-sensor-stm32f103ret6-rev1.1/head-sensor.kicad_pcb (2015-02-16)

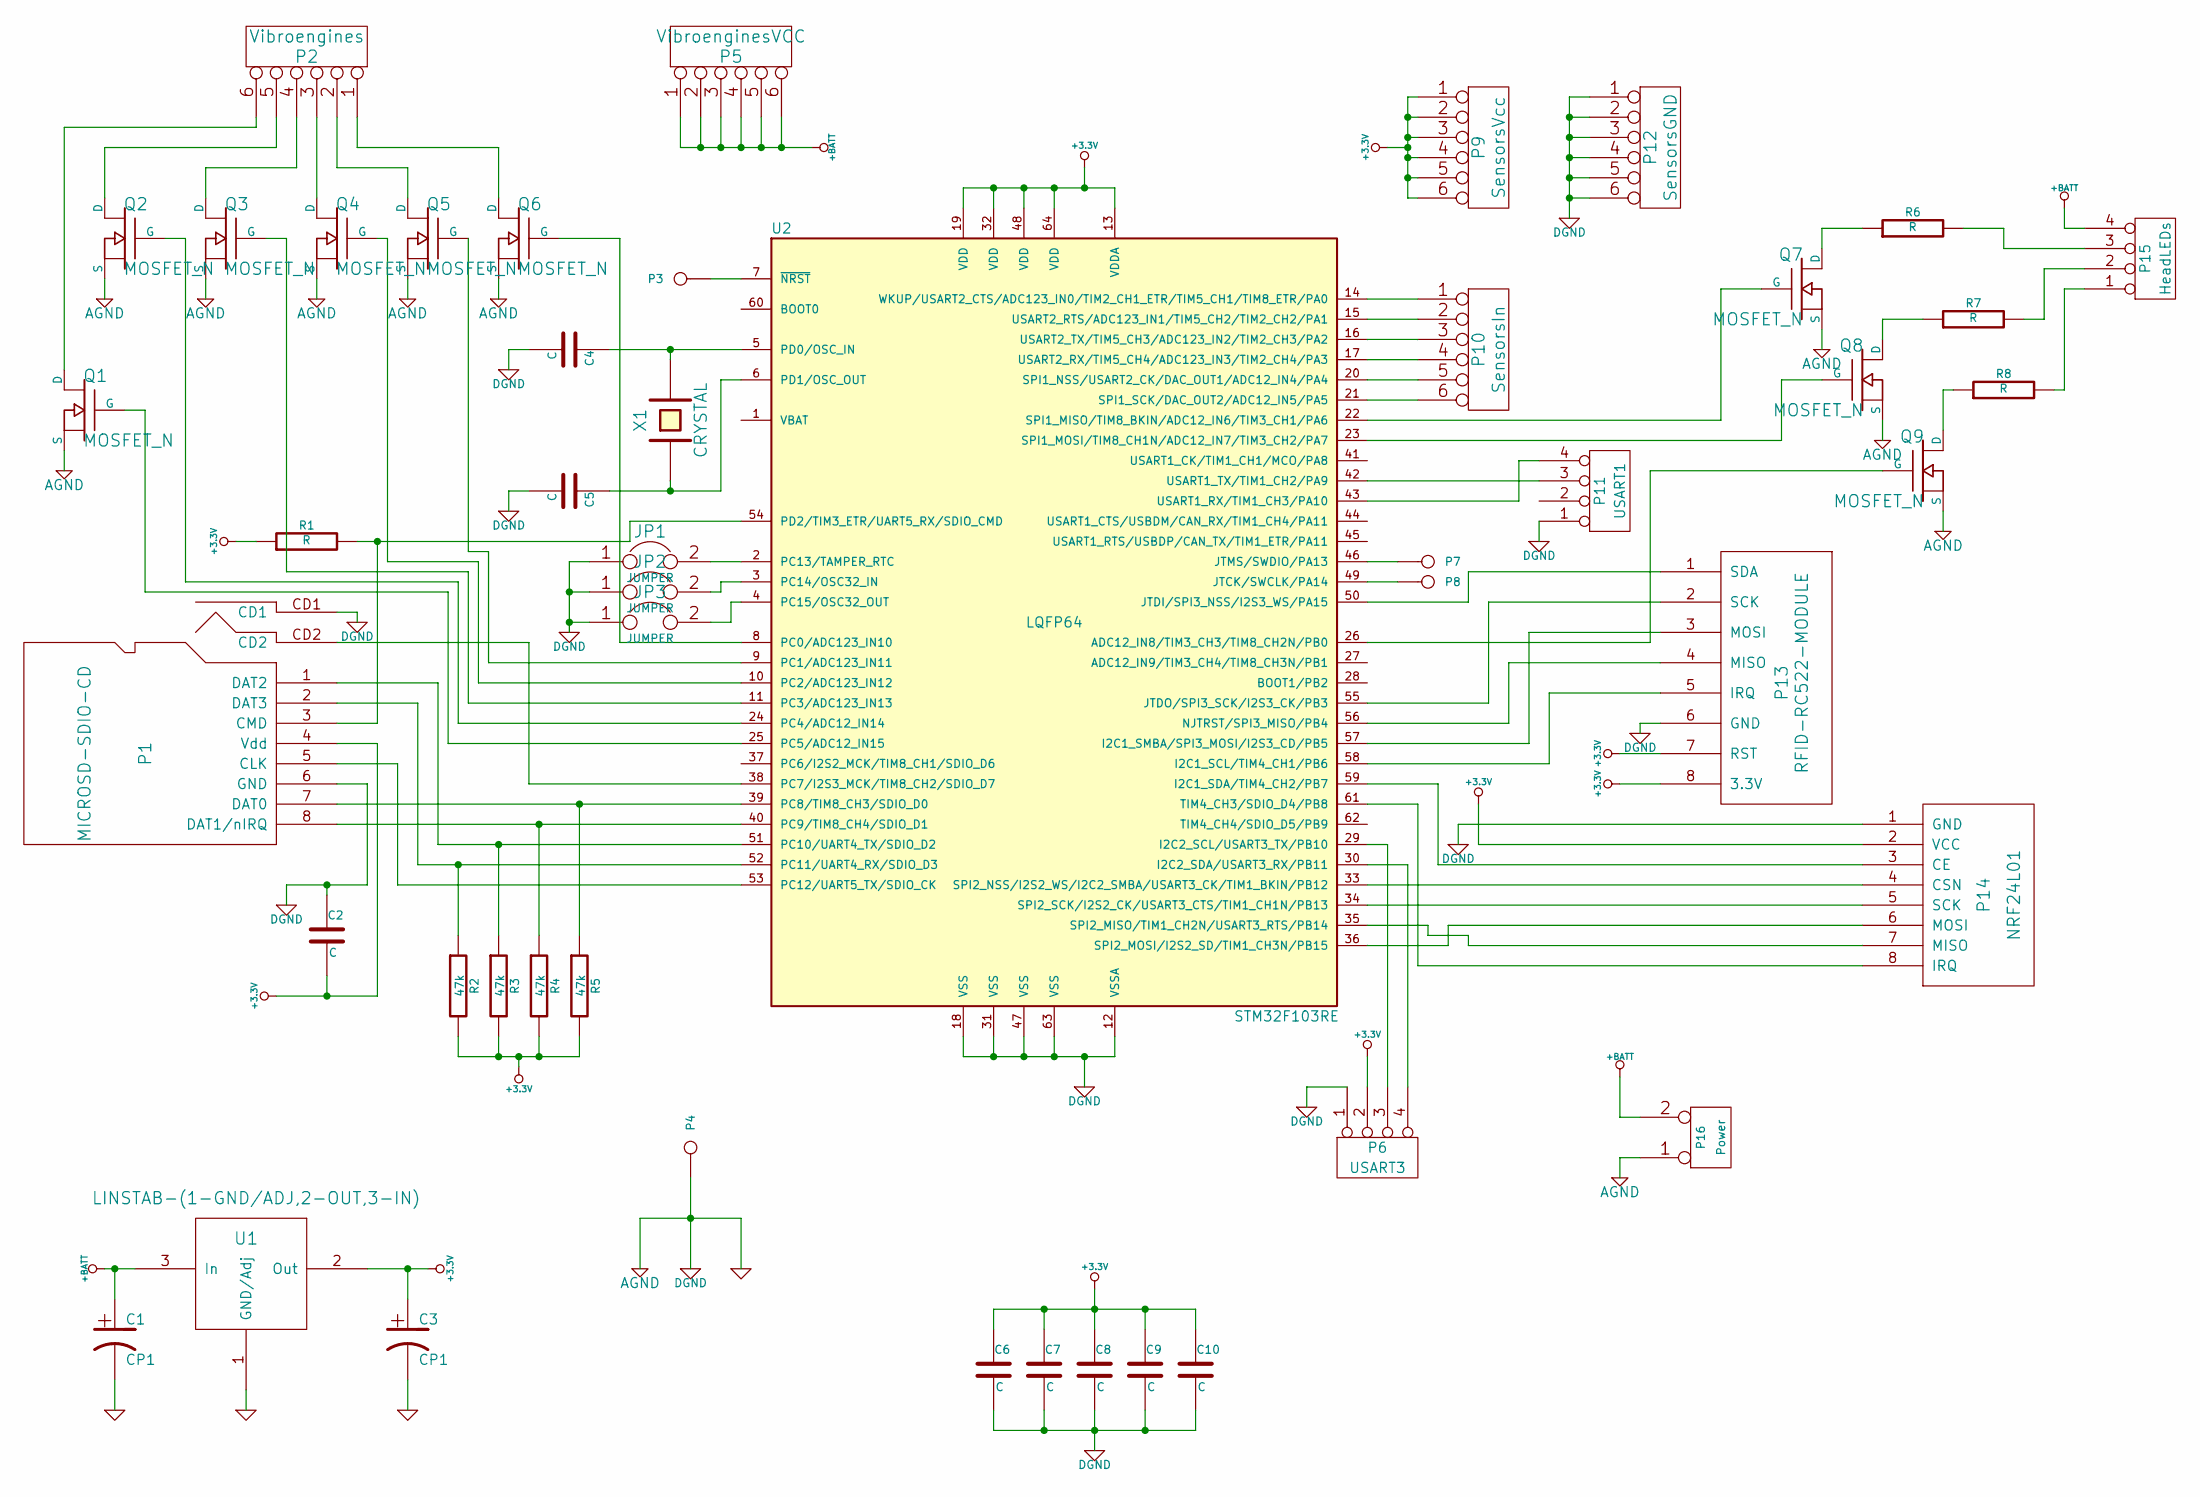
[picture p42: schematic head-sensor.sch, Lazertag head sensor]

Parts:
C1, C3: CP1
C2, C4, C5, C6, C7, C8, C9, C10: C
JP1, JP2, JP3: JUMPER
P1: MICROSD-SDIO-CD
P2: Vibroengines
P3: NRST
P4: SWGND
P5: VibroenginesVCC
P6: USART3
P7: SWDIO
P8: SWCLK
P9: SensorsVcc
P10: SensorsIn
P11: USART1
P12: SensorsGND
P13: RFID-RC522-MODULE
P14: NRF24L01
P15: HeadLEDs
P16: Power
Q1, Q2, Q3, Q4, Q5, Q6, Q7, Q8, Q9: MOSFET_N
R1, R6, R7, R8: R
R2, R3, R4, R5: 47k
U1: LINSTAB-(1-GND/ADJ,2-OUT,3-IN)
U2: STM32F103RE; LQFP64
X1: CRYSTAL

Connections:
+3.3V: C2.2, C3.1, C6.1, C7.1, C8.1, C9.1, C10.1, P1.4 (Vdd), P6.2, P9.1, P9.2, P9.3, P9.4, P9.5, P9.6, P13.7 (RST), P13.8 (3.3V), P14.2 (VCC), R1.1, R2.2, R3.2, R4.2, R5.2, U1.2 (Out), U2.13 (VDDA), U2.19 (VDD), U2.32 (VDD), U2.48 (VDD), U2.64 (VDD)
+BATT: C1.1, P5.1, P5.2, P5.3, P5.4, P5.5, P5.6, P15.4, P16.2 (PM), U1.3 (In)
AGND: C1.2, C2.1, C3.2, C4.2, C5.2, C6.2, C7.2, C8.2, C9.2, C10.2, JP1.1, JP2.1, JP3.1, P1.6 (GND), P1.CD1, P4.1, P6.1, P11.1, P12.1, P12.2, P12.3, P12.4, P12.5, P12.6, P13.6 (GND), P14.1 (GND), P16.1, Q1.S, Q2.S, Q3.S, Q4.S, Q5.S, Q6.S, Q7.S, Q8.S, Q9.S, U1.1 (GND/Adj), U2.12 (VSSA), U2.18 (VSS), U2.31 (VSS), U2.47 (VSS), U2.63 (VSS)
unnamed: Q8.D, R7.1
unnamed: Q7.D, R6.1
unnamed: P15.2, R7.2
unnamed: P15.3, R6.2
unnamed: P2.6, Q1.D
unnamed: P1.8 (DAT1/nIRQ), R4.1, U2.40 (PC9/TIM8_CH4/SDIO_D1)
unnamed: P1.7 (DAT0), R5.1, U2.39 (PC8/TIM8_CH3/SDIO_D0)
unnamed: P2.5, Q2.D
unnamed: Q9.D, R8.1
unnamed: P15.1, R8.2
unnamed: Q4.G, U2.10 (PC2/ADC123_IN12)
unnamed: Q2.G, U2.24 (PC4/ADC12_IN14)
unnamed: Q3.G, U2.11 (PC3/ADC123_IN13)
unnamed: Q5.G, U2.9 (PC1/ADC123_IN11)
unnamed: Q6.G, U2.8 (PC0/ADC123_IN10)
unnamed: P2.1, Q6.D
unnamed: P2.4, Q3.D
unnamed: P2.3, Q4.D
unnamed: P2.2, Q5.D
unnamed: Q1.G, U2.25 (PC5/ADC12_IN15)
unnamed: P13.5 (IRQ), U2.58 (I2C1_SCL/TIM4_CH1/PB6)
unnamed: P13.4 (MISO), U2.56 (NJTRST/SPI3_MISO/PB4)
unnamed: P13.3 (MOSI), U2.57 (I2C1_SMBA/SPI3_MOSI/I2S3_CD/PB5)
unnamed: P6.3, U2.29 (I2C2_SCL/USART3_TX/PB10)
unnamed: P6.4, U2.30 (I2C2_SDA/USART3_RX/PB11)
unnamed: P7.1, U2.46 (JTMS/SWDIO/PA13)
unnamed: P14.3 (CE), U2.59 (I2C1_SDA/TIM4_CH2/PB7)
unnamed: P14.8 (IRQ), U2.61 (TIM4_CH3/SDIO_D4/PB8)
unnamed: P3.1, U2.7 (~NRST)
unnamed: P8.1, U2.49 (JTCK/SWCLK/PA14)
unnamed: P13.1 (SDA), U2.50 (JTDI/SPI3_NSS/I2S3_WS/PA15)
unnamed: P13.2 (SCK), U2.55 (JTDO/SPI3_SCK/I2S3_CK/PB3)
unnamed: P1.5 (CLK), U2.53 (PC12/UART5_TX/SDIO_CK)
unnamed: P1.1 (DAT2), R3.1, U2.51 (PC10/UART4_TX/SDIO_D2)
unnamed: P1.3 (CMD), R1.2, U2.54 (PD2/TIM3_ETR/UART5_RX/SDIO_CMD)
unnamed: P1.2 (DAT3), R2.1, U2.52 (PC11/UART4_RX/SDIO_D3)
unnamed: Q8.G, U2.23 (SPI1_MOSI/TIM8_CH1N/ADC12_IN7/TIM3_CH2/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)
unnamed: P10.1, U2.14 (WKUP/USART2_CTS/ADC123_IN0/TIM2_CH1_ETR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)
unnamed: P10.2, U2.15 (USART2_RTS/ADC123_IN1/TIM5_CH2/TIM2_CH2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)
unnamed: P10.3, U2.16 (USART2_TX/TIM5_CH3/ADC123_IN2/TIM2_CH3/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)
unnamed: P10.4, U2.17 (USART2_RX/TIM5_CH4/ADC123_IN3/TIM2_CH4/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)
unnamed: P10.5, U2.20 (SPI1_NSS/USART2_CK/DAC_OUT1/ADC12_IN4/P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)
unnamed: P10.6, U2.21 (SPI1_SCK/DAC_OUT2/ADC12_IN5/PA5)
unnamed: Q7.G, U2.22 (SPI1_MISO/TIM8_BKIN/ADC12_IN6/TIM3_CH1/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)
unnamed: Q9.G, U2.26 (ADC12_IN8/TIM3_CH3/TIM8_CH2N/PB0)
unnamed: JP3.2, U2.4 (PC15/OSC32_OUT)
unnamed: JP1.2, U2.2 (PC13/TAMPER_RTC)
unnamed: JP2.2, U2.3 (PC14/OSC32_IN)
unnamed: P1.CD2, U2.38 (PC7/I2S3_MCK/TIM8_CH2/SDIO_D7)
unnamed: C4.1, U2.5 (PD0/OSC_IN), X1.2
unnamed: C5.1, U2.6 (PD1/OSC_OUT), X1.1
unnamed: P14.4 (CSN), U2.33 (SPI2_NSS/I2S2_WS/I2C2_SMBA/USART3_CK/TI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)
unnamed: P11.3, U2.42 (USART1_TX/TIM1_CH2/PA9)
unnamed: P14.5 (SCK), U2.34 (SPI2_SCK/I2S2_CK/USART3_CTS/TIM1_CH1N/P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)
unnamed: P11.4, U2.43 (USART1_RX/TIM1_CH3/PA10)
unnamed: P14.7 (MISO), U2.35 (SPI2_MISO/TIM1_CH2N/USART3_RTS/PB14)
unnamed: P14.6 (MOSI), U2.36 (SPI2_MOSI/I2S2_SD/TIM1_CH3N/PB15)

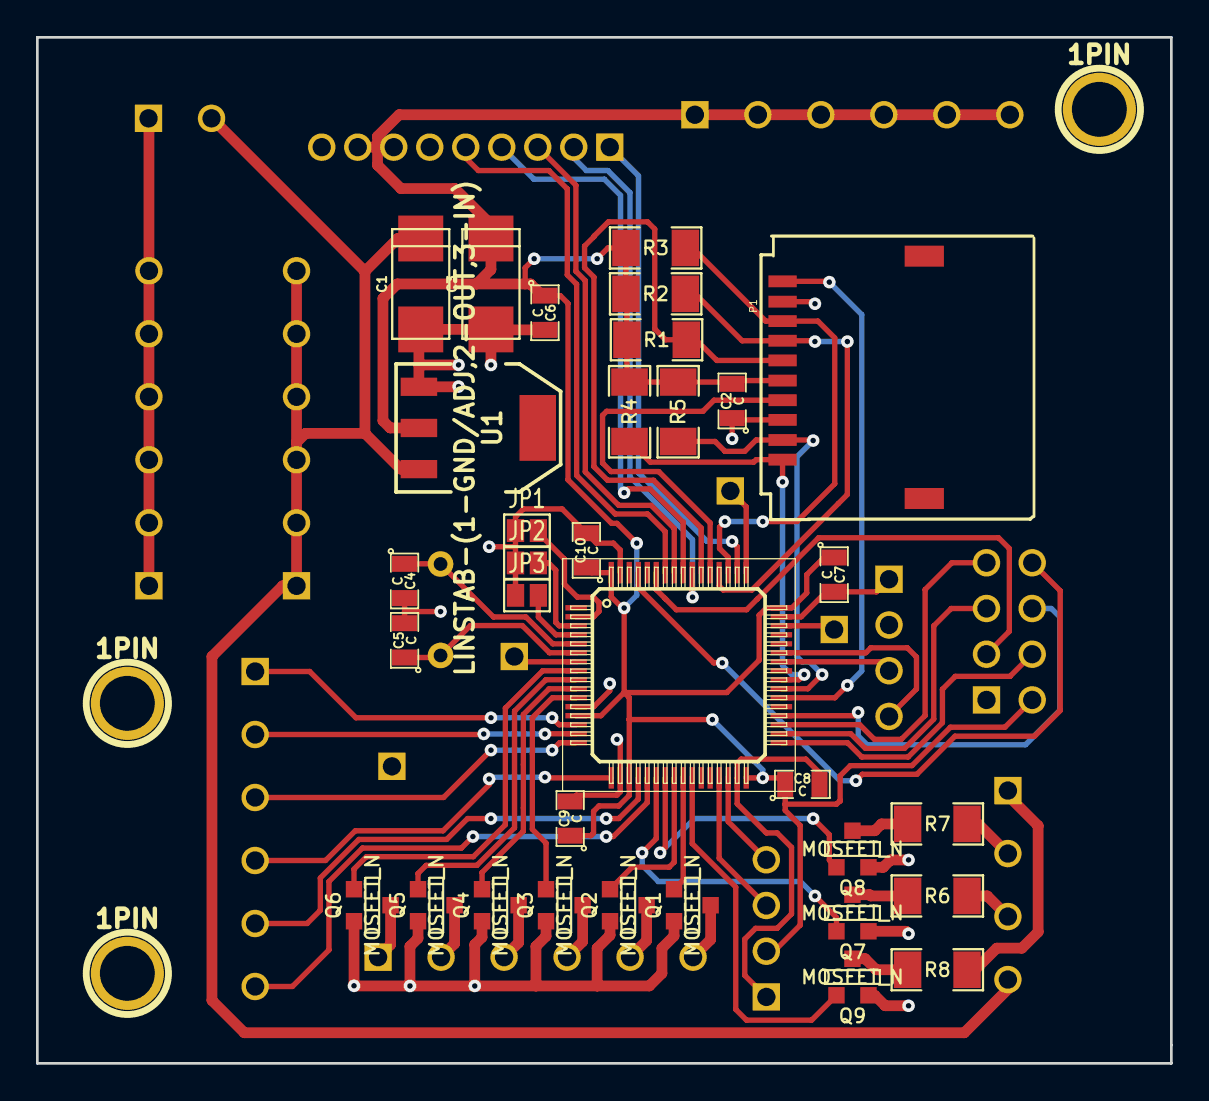
[picture p43: board head-sensor.kicad_pcb from above]

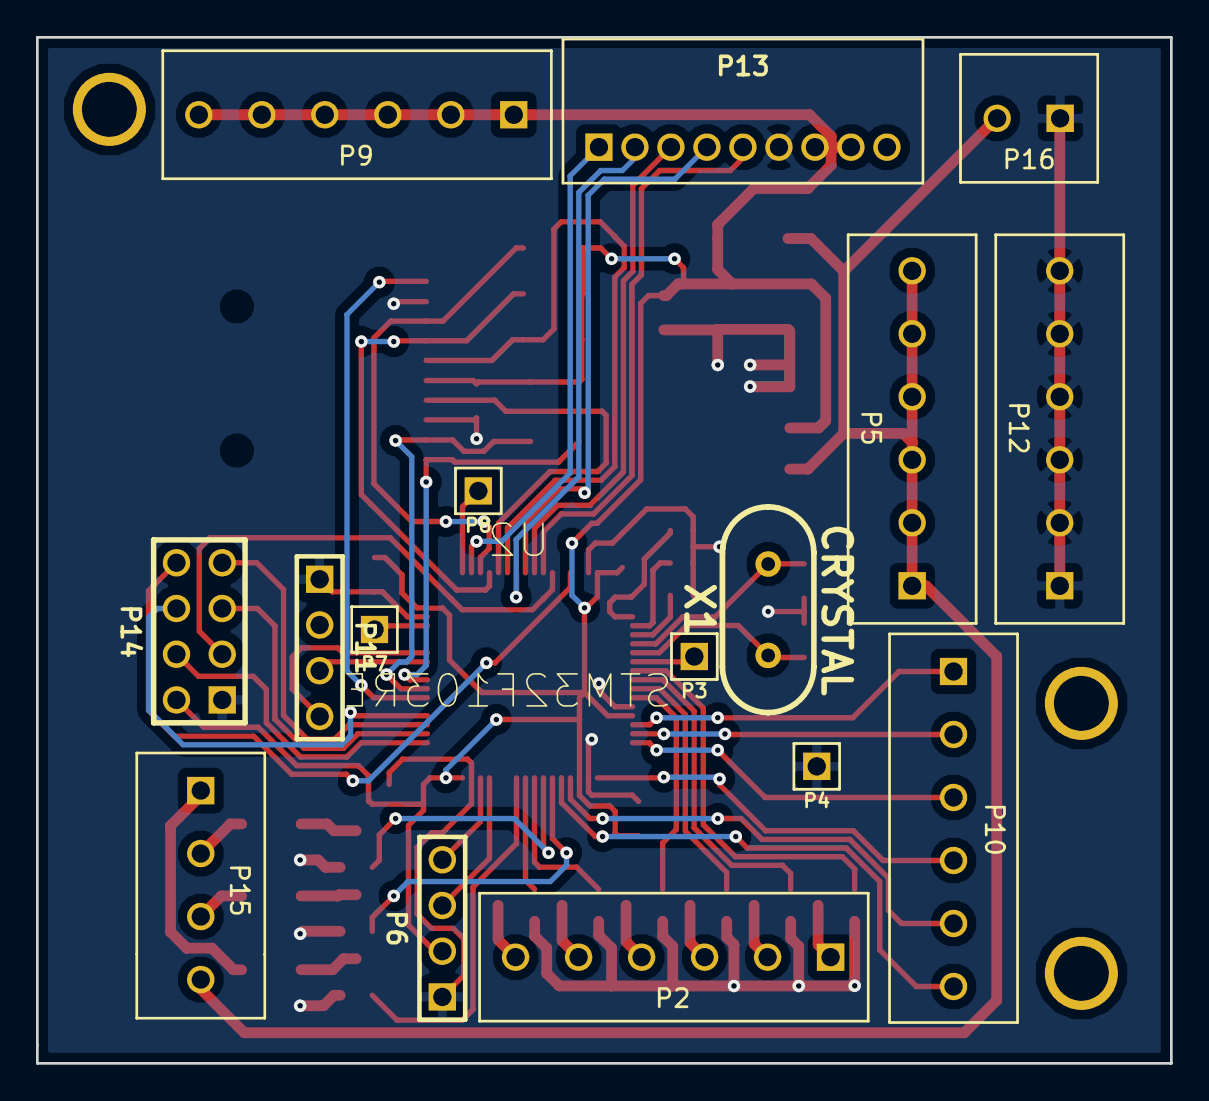
[picture p44: board head-sensor.kicad_pcb from below]

Board: 2 copper layers, 63.0 x 57.0 mm, 52 parts (16 on the bottom side), 60 nets.

Other parts of the board:
1PIN, 1PIN#2, 1PIN#3: P***; 1pin
