DAlexis/caustic-lasertag-system/sdcards/rifle/config.ini

#
# Rifle configuration file
#

slot = 1
weightInSlot = 0

damageMin = 25
damageMax = 25
firePeriod = 100000
shotDelay = 0

jamProb = 0
criticalProb = 0
criticalCoeff = 1

semiAutomaticAllowed = true
automaticAllowed = true

reloadIsMagazineSmart = false
reloadNeedMagDisconnect = false
reloadNeedMagChange = false
reloadNeedBolt = true
reloadPlaySound = true

magazinesCountMax = 10
magazinesCountStart = 10

bulletsInMagazineMax = 30
bulletsInMagazineStart = 30
reloadingTime = 3000000

heatPerShot = 0
heatLossPerSec = 0

outputPower = 100

devAddr = 20.0.10
headSensorAddr = 10.0.10
deviceName = Rifle 1

supplyVoltageMin = 3.7
supplyVoltageMax = 4.2
adcCalibrationCoeff = 2.0
