DAlexis/caustic-lasertag-system/sdcards/rifle/pinout.ini

fireButton_port   =   0
fireButton_pin    =   0

reloadButton_port =   0
reloadButton_pin  =   1

automaticButton_port      =   2
automaticButton_pin       =   1

semiAutomaticButton_port  =   2
semiAutomaticButton_pin   =   0

magazine1Sensor_port = 2
magazine1Sensor_pin  = 2

magazine2Sensor_port = 2
magazine2Sensor_pin  = 3

flash_port = 0
flash_pin  = 3

vibro_port = 0
vibro_pin  = 2

IRPowerLevel1Channel = 1
IRPowerLevel2Channel = 2
IRPowerLevel3Channel = 3
IRPowerLevel4Channel = 4

display = ssd1306
#display = lcd5110
#display = none
