DAlexis/caustic-lasertag-system/sdcards/rifle/pinout-monolith.ini

fireButton_port   =   0
fireButton_pin    =   0

reloadButton_port =   1
reloadButton_pin  =   2

automaticButton_port      =   2
automaticButton_pin       =   7

semiAutomaticButton_port  =   1
semiAutomaticButton_pin   =   9

magazine1Sensor_port = 0
magazine1Sensor_pin  = 11

magazine2Sensor_port = 0
magazine2Sensor_pin  = 12

flash_port = 1
flash_pin  = 11

vibro_port = 0
vibro_pin  = 1

IRPowerLevel1Channel = 4
IRPowerLevel2Channel = 3
