DAlexis/caustic-lasertag-system/sdcards/bluetooth-bridge/bb-config.ini

devAddr = 50.0.10
deviceName = CausticBridge
bluetoothPin = 1234

supplyVoltageMin = 3.7
supplyVoltageMax = 4.2
adcCalibrationCoeff = 2.0
