DAlexis/caustic-lasertag-system/cpp-sources/universal-device/high-level/src/bluetooth-bridge/bluetooth-bridge.cpp

/*
*    Copyright (C) 2016 by Aleksey Bulatov
*
*    This file is part of Caustic Lasertag System project.
*
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
*    @license GPL-3.0+ <http://spdx.org/licenses/GPL-3.0+>
*/


#include "bluetooth-bridge/bluetooth-bridge.hpp"
#include "core/logging.hpp"
#include "core/power-monitor.hpp"
#include "core/string-utils.hpp"
#include "dev/nrf24l01.hpp"
#include "network/broadcast.hpp"

#include <string.h>

using namespace Bluetooth;

BluetoothBridgePackageTimings bluetoothBridgePackageTimings;

BluetoothBridge::BluetoothBridge(INetworkLayer *existingNetworkLayer) :
		AnyONCDeviceBase(existingNetworkLayer)
{
}

void BluetoothBridge::initAsSecondaryDevice(const Pinout& pinout, bool isSdcardOk)
{
    UNUSED_ARG(pinout);
    m_bbStager.stage("Init");
    debug << "Bluetooth bridge initialization";

    // default address for bluetooth bridge without SD-card
    deviceConfig.devAddr.address[0] = 50;
    deviceConfig.devAddr.address[1] = 50;
    deviceConfig.devAddr.address[2] = 50;

    if (isSdcardOk)
    {
        if (!m_aggregator.readIni("bb-config.ini"))
        {
            error << "Cannot read config file, so setting default values";
            config.setDefault();
        }
    } else {
        warning << "Bluetooth bridge operate without sd-card, it will use default settings";
    }

    m_networkClient->connectPayloadReceiver(this);

    /*
    m_workerToNetwork.setStackSize(512);
    m_workerToNetwork.run();*/

    m_toBluetoothTask.run();

    configureBluetooth();
}

void BluetoothBridge::init(const Pinout& pinout, bool isSdcardOk)
{
    UNUSED_ARG(pinout);

    initAsSecondaryDevice(pinout, isSdcardOk);

    //NetworkLayer::instance().enableRegularNRFReinit();

	m_tasksPool.add(
			[this] { m_powerMonitor.interrogate(); },
			100000
	);

	m_tasksPool.setStackSize(256);
	m_tasksPool.run();
}

void BluetoothBridge::setDefaultPinout(Pinout& pinout)
{
    UNUSED_ARG(pinout);
}

bool BluetoothBridge::checkPinout(const Pinout& pinout)
{
    UNUSED_ARG(pinout);
	return true;
}

void BluetoothBridge::configureBluetooth()
{
	m_bluetoothPort = UARTs->get(IUARTSPool::UART2);

	// First, configuring HC-05 bluetooth module to have proper name, UART speed and password
	m_configurator.init(IOPins->getIOPin(IIOPin::PORTA, 1), m_bluetoothPort);

	info << "Determining speed of UART for HC-05";
	HC05Configurator::HC05Result result = m_configurator.selectSpeed();
	if (result != HC05Configurator::HC05Result::ok)
	{
		error << "Cannot determine HC-05 speed. Somebody might have configured "
		         "it by external tool. Bluetooth bridge will not operate! Error: " << HC05Configurator::parseResult(result);
	}

	m_configurator.configure();
	m_configurator.leaveAT();

	// Then we can initialize data receiving system and run worker that put data to bluetooth
	m_bluetoothPort->setBlockSize(1);
	m_bluetoothPort->setRXDoneCallback(
		[this](uint8_t* buffer, uint16_t size)
		{
			UNUSED_ARG(size);
			receiveBluetoothOneByteISR(buffer[0]);
		}
	);

	m_bluetoothPort->init(HC05Configurator::uartTargetSpeed);
}

void BluetoothBridge::receive(DeviceAddress sender, const uint8_t* payload, uint16_t payloadLength)
{
	m_bbStager.stage("receivePackage");
    debug << "[net=>bt out queue] Package from "
    		<< ADDRESS_TO_STREAM(sender)
			<< ", payload size = " << payloadLength
			<< ", bt queue size = " << m_messagesToBluetooth.size();
    m_bluetoothMsgCreator.clear();
    m_bluetoothMsgCreator.setSender(std::move(sender));
    m_bluetoothMsgCreator.addData(payloadLength, payload);
    m_bluetoothMsgCreator.msg().setChecksum();
    Bluetooth::Message *msg = new Bluetooth::Message();
    *msg = m_bluetoothMsgCreator.msg();


    if (hasFreeSpaceInQueues())
    {
    	ScopedLock<Mutex> lck(m_messagesToBluetoothMutex);
    	m_messagesToBluetooth.push(msg);
    	//debug << "To bluetooth queue size = " << m_messagesToBluetooth.size();
    } // else drop :(

	//delete msg;


}

void BluetoothBridge::receiveBluetoothOneByteISR(uint8_t byte)
{
	m_receiver.readByte(byte);
	if (m_receiver.ready())
	{
		m_bbStager.stage("receiver ready");
		receiveBluetoothPackageISR(&m_receiver.get());
		m_receiver.reset();
	}
}

void BluetoothBridge::receiveBluetoothPackageISR(Bluetooth::Message* msg)
{
	if (!msg->isChecksumCorrect())
		return;

	if (!hasFreeSpaceInQueues())
		return; // Drop package :(

	Bluetooth::Message *msgToSend = new Bluetooth::Message();
	*msgToSend = *msg;
	// No need in synchronization primitive: we are in interrupt
	m_messagesToNetwork.push(msgToSend);

	/*
	m_workerToNetwork.addFromISR(
		[this, msgToSend] ()
		{
			//ScopedLock<Mutex> lck(m_processingMutex);
			sendNetworkPackage(msgToSend->address, msgToSend->payload, msgToSend->payloadLength());
			delete msgToSend;
		}
	);*/
}

void BluetoothBridge::sendBluetoothMessage(Bluetooth::Message* msg)
{
	m_bbStager.stage("sendBluetoothMessage");
	debug << "Sending to bluetooth";
	msg->print();
	// Transmitting to bluetooth module and waiting while transmit is done
	m_bluetoothPort->transmit(reinterpret_cast<uint8_t*>(msg), msg->length);
	while (m_bluetoothPort->txBusy()) { }
}

void BluetoothBridge::sendNetworkPackage(DeviceAddress addr, uint8_t* payload, uint16_t size)
{
	m_bbStager.stage("sendNetworkPackage");
	debug << "[bt in queue=>net] Sending, target: " << ADDRESS_TO_STREAM(addr) << "payload size: " << size;

	// Sending message body as is
	if (Broadcast::isBroadcast(addr))
	{
		// We need special timings for broadcasts
	    m_networkClientSender->send(
	    		addr,
                payload,
				size,
                true,
                nullptr,
                bluetoothBridgePackageTimings.broadcast
        );
	} else {
	    // Not broadcast packages are with default timings
		m_networkClientSender->send(
	    		addr,
				payload,
				size,
	            true
	    );
	}
}

void BluetoothBridge::mainLoop()
{
	for (;;)
	{
		if (m_messagesToBluetooth.empty() && m_messagesToNetwork.empty())
		{
			Kernel::yield();
			continue;
		}

		// Sending to bluetooth
		if (!m_messagesToBluetooth.empty())
		{
			Bluetooth::Message* msg = nullptr;
			{
				ScopedLock<Mutex> lck(m_messagesToBluetoothMutex);
				msg = m_messagesToBluetooth.front();
				m_messagesToBluetooth.pop();
			}

			sendBluetoothMessage(msg);
			delete msg;
		}

		// Sending to network
		if (!m_messagesToNetwork.empty())
		{
			// Critical section to prevent entering interrupt here
			CritialSection cs; cs.lock();
				Bluetooth::Message* msg = m_messagesToNetwork.front();
				m_messagesToNetwork.pop();
			cs.unlock();

			sendNetworkPackage(msg->address, msg->payload, msg->payloadLength());
			delete msg;
		}
	}
}

bool BluetoothBridge::hasFreeSpaceInQueues()
{
	uint32_t tn = m_messagesToNetwork.size();
	//trace << "To network queue size = " << tn;
	uint32_t tb = m_messagesToBluetooth.size();
	//trace << "To bluetooth queue size = " << tb;
	return tn+tb < queuesSizeMax;
}
