DAlexis/caustic-lasertag-system/cpp-sources/universal-device/high-level/include/rifle/rifle.hpp

/*
*    Copyright (C) 2016 by Aleksey Bulatov
*
*    This file is part of Caustic Lasertag System project.
*
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
*    @license GPL-3.0+ <http://spdx.org/licenses/GPL-3.0+>
*/

#ifndef LAZERTAG_RIFLE_INCLUDE_LOGIC_RIFLE_HPP_
#define LAZERTAG_RIFLE_INCLUDE_LOGIC_RIFLE_HPP_

#include <any-device/device.hpp>
#include <dev/RC522-wrapper.hpp>
#include "any-device/any-rcsp-device-base.hpp"
#include "core/device-initializer.hpp"
#include "core/os-wrappers.hpp"
#include "dev/buttons.hpp"
#include "dev/wav-player.hpp"
#include "dev/ssd1306-display.hpp"
#include "dev/key-sequence.hpp"
#include "ir/ir-physical.hpp"
#include "ir/ir-presentation.hpp"
#include "rcsp/operation-codes.hpp"
#include "rifle/rifle-config.hpp"
#include "rifle/rifle-state.hpp"
#include "rifle/resources.hpp"
#include "rifle/rifle-base-types.hpp"
#include "rifle/rifle-display.hpp"
#include "rifle/rifle-rfid-controller.hpp"
#include "network/network-client.hpp"

#include <stdint.h>


class Rifle : public AnyRCSPClientDeviceBase
{
public:
	Rifle();

	void init(const Pinout& pinout, bool isSdcardOk) override;
	void setDefaultPinout(Pinout& pinout) override;
	bool checkPinout(const Pinout& pinout) override;

	FUNCTION_NP(ConfigCodes::Rifle::Functions, Rifle, rifleTurnOn, m_aggregator);
	FUNCTION_NP(ConfigCodes::Rifle::Functions, Rifle, rifleTurnOff, m_aggregator);
	FUNCTION_NP(ConfigCodes::Rifle::Functions, Rifle, rifleReset, m_aggregator);    ///< Make rifle absolutely new
	FUNCTION_NP(ConfigCodes::Rifle::Functions, Rifle, rifleRespawn, m_aggregator);  ///< Do all things than needed on respawn (+play sound)
	FUNCTION_NP(ConfigCodes::Rifle::Functions, Rifle, rifleDie, m_aggregator);      ///< Say to rifle that player was killed

	/// Heartbeat head sensor -> rifle
	FUNCTION_1P(ConfigCodes::Rifle::Functions, Rifle, headSensorToRifleHeartbeat, m_aggregator);
	FUNCTION_NP(ConfigCodes::Rifle::Functions, Rifle, rifleWound, m_aggregator);
	FUNCTION_NP(ConfigCodes::Rifle::Functions, Rifle, rifleRFIDProgramHSAddr, m_aggregator);
	FUNCTION_NP(ConfigCodes::Rifle::Functions, Rifle, rifleRFIDProgramServiceCard, m_aggregator);

	FUNCTION_1P(ConfigCodes::Rifle::Functions, Rifle, riflePlayEnemyDamaged, m_aggregator);      ///< Play enemy damaged sound
	FUNCTION_1P(ConfigCodes::Rifle::Functions, Rifle, rifleShock, m_aggregator);
	FUNCTION_1P(ConfigCodes::Rifle::Functions, Rifle, rifleChangeHS, m_aggregator);

	RifleConfiguration config{m_aggregator};
	RifleOwnerConfiguration rifleOwner{m_aggregator};
	RifleState state{&config, m_aggregator};
	//DeviceParameters device;

	PlayerPartialState playerState{config.headSensorAddr, *m_networkClientSender, &m_aggregator};

private:

	constexpr static TimeInterval maxNoHeartbeatDelay = 2500000;
	constexpr static TimeInterval heartbeatPeriod = 400000;

	struct PinoutTexts
	{
		constexpr static const char *trigger = "fireButton";
		constexpr static const char *reload = "reloadButton";
		constexpr static const char *automatic = "automaticButton";
		constexpr static const char *semiAutomatic = "semiAutomaticButton";
		constexpr static const char *mag1Sensor = "magazine1Sensor";
		constexpr static const char *mag2Sensor = "magazine2Sensor";
		constexpr static const char *flash = "flash";
		constexpr static const char *vibro = "vibro";
	};

	struct WeaponState
	{
		constexpr static uint8_t magazineEmpty = 0;
		constexpr static uint8_t magazineRemoved = 1;
		constexpr static uint8_t magazineReturned = 2;
		constexpr static uint8_t otherMagazineInserted = 3;
		constexpr static uint8_t reloading = 4;
		constexpr static uint8_t ready = 5;
	};

	void loadConfig();
	void initSounds();
	void initSequenceDetectors();

	void rfidSwitchToRead();

	void makeShot(bool isFirst);
	void prepareAndSendShotMsg();
	void distortBolt(bool isFirst);
	void magazineSensor(bool isConnected, uint8_t sensorNumber, bool isFirst);
	uint8_t getCurrentMagazineNumber();

	void reloadAndPlay();
	void detectReloadAndMagsState();

	/**
	 * To use inside HS-to-rifle commands to check that command is from actual head sensor
	 */
	bool isCommandFromActualHS();

	bool isReloading();
	bool isSafeSwitchSelected();
	bool isShocked();
	bool isHSConnected();

	void updatePlayerState();

	void playDamagerNotification(uint8_t state);
	void scheduleDamageNotification(uint8_t state);
	void checkHeartBeat();

	void cardOperationDoneCallback(RifleRFIDController::Mode mode);

	void sendHeartbeatToHS();

	/// This function could be called any time when head sensor is connected. Double calling does not hurt anything
	void onHSConnected();
	void onHSDisconnected();

	ButtonManager* m_fireButton = nullptr;
	ButtonManager* m_reloadButton = nullptr;
	ButtonManager* m_automaticFireSwitch = nullptr;
	ButtonManager* m_semiAutomaticFireSwitch = nullptr;
	ButtonManager* m_magazine1Sensor = nullptr;
	ButtonManager* m_magazine2Sensor = nullptr;
	IIOPin* m_vibroEngine = nullptr;
	IIOPin* m_fireFlash = nullptr;

	KeySequenceDetector m_writeCardSeqDetector;

	IIRTransmitter *m_irPhysicalTransmitter = nullptr;
	IIRPresentationTransmitter *m_irPresentationTransmitter = nullptr;

	SoundPlayer m_systemReadySound;
	SoundPlayer m_RFIDCardReaded;
	SoundPlayer m_connectedToHeadSensorSound;
	SoundPlayer m_shootingSound;
	SoundPlayer m_reloadingSound;
	SoundPlayer m_noAmmoSound;
	SoundPlayer m_noMagazines;
	SoundPlayer m_respawnSound;
	SoundPlayer m_dieSound;
	SoundPlayer m_woundSound;
	SoundPlayer m_enemyDamaged;
	SoundPlayer m_enemyKilled;
	SoundPlayer m_friendDamaged;
	SoundPlayer m_noHeartbeat;
	SoundPlayer m_noShockedShooting;
	SoundPlayer m_hsSwitchRejected;
	SoundPlayer m_rfidProgrammingInProcess;

	PackageId m_registerWeaponPAckageId = 0;

	uint8_t m_state = WeaponState::ready;
	uint8_t m_currentMagazineNumber = 0; ///< zero means no magazine

	Interrogator m_buttonsInterrogator{"BtnsIntr"};
	TasksPool m_tasksPool{"RiflPool"};
	Time m_lastHSHeartBeat = 0;

	/// If current time > m_unshockTime, player is not shocked now
	Time m_unshockTime = 0;
	RifleDisplayBase* m_display = nullptr;

	RC552Frontend m_mfrcWrapper;
	RifleRFIDController m_rfidController{m_mfrcWrapper, m_aggregator};
};

#endif /* LAZERTAG_RIFLE_INCLUDE_LOGIC_RIFLE_HPP_ */
