DAlexis/caustic-lasertag-system/cpp-sources/universal-device/high-level/src/dev/wav-player.cpp

/*
*    Copyright (C) 2016 by Aleksey Bulatov
*
*    This file is part of Caustic Lasertag System project.
*
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
*    @license GPL-3.0+ <http://spdx.org/licenses/GPL-3.0+>
*/

#include "dev/wav-player.hpp"
#include "dev/random.hpp"
#include "core/logging.hpp"
#include "core/string-utils.hpp"
#include <stdio.h>
#include <string.h>
#include <sys/stat.h>

SINGLETON_IN_CPP(WavPlayer)

WavPlayer::WavPlayer()
{
	debug << "Creating audio buffers";
	m_buffer1 = new SoundSample[audioBufferSize];
	m_buffer2 = new SoundSample[audioBufferSize];
	m_tempBuffer = new SoundSample[audioBufferSize];
	trace << "Testing audio buffers";
	for (unsigned int i=0; i<audioBufferSize; i++)
	{
		m_buffer1[i] = 0xFFFF;
		m_buffer2[i] = 0xFFFF;
		m_tempBuffer[i] = 0xFFFF;
	}
	debug << "Done";
	m_currentBuffer = m_buffer1;
	m_nextBuffer = m_buffer2;

	m_loader.setStackSize(512);
	m_loader.setName("WavLdr");

}

WavPlayer::~WavPlayer()
{
	delete[] m_buffer1;
	delete[] m_buffer2;
	delete[] m_tempBuffer;
}


void WavPlayer::init()
{
	m_fragmentPlayer = fragmentPlayerCreator->get();
	m_fragmentPlayer->init();
	m_fragmentPlayer->setFragmentDoneCallback(std::bind(&WavPlayer::fragmentDoneCallback, this, std::placeholders::_1));
	m_loader.run();

	// Prepairing buffers
	silenceToBuffer(m_currentBuffer);
	silenceToBuffer(m_nextBuffer);
	// Starting infinite playback
	m_fragmentPlayer->setFragmentSize(audioBufferSize);
}

void WavPlayer::silenceToBuffer(SoundSample* buffer)
{
	for (unsigned int i=0; i<audioBufferSize; i++)
		buffer[i] = INT16_MAX >> 4;
	//buffer[0] = buffer[1] = INT16_MAX >> 4 + 1000;
}

bool WavPlayer::openFile(uint8_t channel)
{
	// If we already playing on this channel
	if (m_contexts[channel].fileIsOpened)
	{
		fclose(m_contexts[channel].file);
		m_contexts[channel].fileIsOpened = false;
	}

	debug << "Opening file...";
	//res = f_open(&m_contexts[channel].file, m_contexts[channel].filename, FA_OPEN_EXISTING | FA_READ);
	m_contexts[channel].file = fopen(m_contexts[channel].filename, "r");
    if (!m_contexts[channel].file)
	{
        error << "fopen returned error " << errno;
		return false;
	}

	//debug << "ok";
	m_contexts[channel].fileIsOpened = true;

	if (!m_contexts[channel].readHeader())
	{
		fclose(m_contexts[channel].file);
		error << "Invalid file header";
		return false;
	}

	//trace << "File header is ok";
	m_contexts[channel].totalReaded = 0;

	// Adding first fragment from file to next buffer
	return loadFragment(m_nextBuffer, channel);
}

Result WavPlayer::play(const char* fileName, uint8_t channel)
{
	// To start playing we should add task to queue
	if (!m_fragmentPlayerReady)
	{
		m_fragmentPlayerReady = true;
		m_fragmentPlayer->playFragment(m_currentBuffer);
	}
	m_contexts[channel].filename = fileName;

	// Adding task to open file
	m_loader.add(
			[this, channel](){ openFile(channel); }
	);
	return Result();
}

void WavPlayer::fragmentDoneCallback(SoundSample* oldBuffer)
{
	UNUSED_ARG(oldBuffer);
	std::swap(m_currentBuffer, m_nextBuffer);
	m_fragmentPlayer->playFragment(m_currentBuffer);

	// Telling to clear buffer
	m_loader.addFromISR(
			[this]() { silenceToBuffer(m_nextBuffer); }
	);

	// Telling to add sound from all channels to buffers
	for (int i=0; i<channelsCount; i++)
	{
		m_loader.addFromISR(
				[this, i] () { loadFragment(m_nextBuffer, i); }
		);
	}
}

bool WavPlayer::ChannelContext::readHeader()
{
    uint32_t readed = fread(&header, 1, sizeof(header), file);
	if (ferror(file))
	{
		error << "Cannot read header from file";
		return false;
	}

	if (readed != sizeof(header))
	{
		error << "Incomplete wav file";
		return false;
	}

	//if (m_verbose) printInfo();

	// Validating m_header
	if (strncmp(header.riff, "RIFF", 4) != 0)
	{
		error << "Invalid format: not RIFF";
		return false;
	}
	if (header.audio_format != 1)
	{
		error << "Invalid audio format: " << header.audio_format << " - Only PCM audio supported";
		return false;
	}
	if (header.num_channels != 1)
	{
		error << "Invalid channels count: " << header.num_channels << " - Only mono sound supported";
		return false;
	}
	if (header.bits_per_sample != 16)
	{
		error << "Invalid bits per sample rate: " << header.bits_per_sample << " - Only 16 supported";
		return false;
	}
	return true;
}

bool WavPlayer::loadFragment(SoundSample* buffer, uint8_t channel)
{
	//trace << "loadig fragment...";
	if (!m_contexts[channel].fileIsOpened)
	{
		//error << "Attempt to load fragment from closed file";
		return false;
	}

    uint32_t bytesReaded = 0;
	int16_t *tmpPrt = reinterpret_cast<int16_t *>(m_tempBuffer);

	// For some unknown reason, f_read does not read more about 1k and crashes
	/// @todo increase blockSize to maximum

	uint16_t sizeToRead = std::min(
			audioBufferSize*sizeof(int16_t),
			m_contexts[channel].header.subchunk2_size - m_contexts[channel].totalReaded
	);

    bytesReaded = fread(tmpPrt, 1, sizeToRead, m_contexts[channel].file);
    int err = ferror(m_contexts[channel].file);
    if (err)
	{
        error << "Cannot read fragment from file: " << err;
        fclose(m_contexts[channel].file);
		return false;
    }

	m_contexts[channel].totalReaded += bytesReaded;

    if (bytesReaded < sizeToRead || feof(m_contexts[channel].file))
	{
		// We readed till file's end, so we can close it
		//trace << "file's end: " << m_contexts[channel].totalReaded;
        fclose(m_contexts[channel].file);
		m_contexts[channel].fileIsOpened = false;
	}

    uint32_t samplesReaded = bytesReaded / sizeof(int16_t);

	for (unsigned int i=samplesReaded; i<audioBufferSize; i++)
	{
		tmpPrt[i] = 0;
	}

	// Now we have array of int16 samples so we need to add it to buffer
	for (unsigned int i=0; i<audioBufferSize; i++)
	{
		buffer[i] += tmpPrt[i] >> 4;
	}

	return true;
}

/////////////////////////
// SoundPlayer
void SoundPlayer::addVariant(const char* filename)
{
	m_variants.push_back(filename);
}

void SoundPlayer::addVariant(std::string& filename)
{
	m_variants.push_back(filename);
}

void SoundPlayer::addVariant(std::string&& filename)
{
	m_variants.push_back(filename);
}

void SoundPlayer::readVariants(const char* filenamePrefix, const char* filenameSuffix, uint8_t channel)
{
	m_channel = channel;
	unsigned int number = 0;
	char buff[10];
	bool notFound = false;
    struct stat st;
	do {
		sprintf(buff, "%u", ++number);
		std::string nextFilename = std::string(filenamePrefix) + buff + filenameSuffix;
        if (stat(nextFilename.c_str(), &st) == 0)
		{
			addVariant(nextFilename);
		} else
			notFound = true;
	} while (!notFound);
	debug << filenamePrefix << "X" << filenameSuffix << " - " << number-1 << " found";
}

void SoundPlayer::play()
{
	if (m_variants.empty())
	{
		warning << "No sound set";
		return;
	}
	unsigned int rnd = Random::random(m_variants.size()-1);
	debug << "Playing variant " << rnd;
	WavPlayer::instance().play(m_variants[rnd].c_str(), m_channel);
}
