DAlexis/caustic-lasertag-system/cpp-sources/universal-device/high-level/src/hw/uart.cpp

/*
*    Copyright (C) 2016 by Aleksey Bulatov
*
*    This file is part of Caustic Lasertag System project.
*
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
*    @license GPL-3.0+ <http://spdx.org/licenses/GPL-3.0+>
*/


#include "hw/uart-hw.hpp"
#include "core/logging.hpp"
#include "utils/macro.hpp"

// For STM32 HAL written in C, this global handlers should exist
extern UART_HandleTypeDef huart1;
extern UART_HandleTypeDef huart2;
extern UART_HandleTypeDef huart3;

UARTSPool uartsPool;
IUARTSPool* UARTs = &uartsPool;

UARTManager::UARTManager(uint8_t portNumber)
{
	switch (portNumber)
	{
	case IUARTSPool::UART1:
		m_huart = &huart1;
		m_instance = USART1;
		break;
	case IUARTSPool::UART2:
		m_huart = &huart2;
		m_instance = USART2;
		break;
	case IUARTSPool::UART3:
		m_huart = &huart3;
		m_instance = USART3;
		break;
	default:
		error << "Cannot control usart " << portNumber;
		return;
	}
}

void UARTManager::init(uint32_t baudrate, bool useHalfDuplex)
{
	m_halfDuplex = useHalfDuplex;
	m_huart->Instance = m_instance;
	m_huart->Init.BaudRate = baudrate;
	m_huart->Init.WordLength = UART_WORDLENGTH_8B;
	m_huart->Init.StopBits = UART_STOPBITS_1;
	m_huart->Init.Parity = UART_PARITY_NONE;
	m_huart->Init.Mode = UART_MODE_TX_RX;
	m_huart->Init.HwFlowCtl = UART_HWCONTROL_NONE;
	m_huart->Init.OverSampling = UART_OVERSAMPLING_16;

	if (m_halfDuplex)
	{
		HAL_HalfDuplex_Init(m_huart);
	} else {
		HAL_UART_Init(m_huart);
	}

	if (m_halfDuplex)
		HAL_HalfDuplex_EnableReceiver(m_huart);
	HAL_UART_Receive_IT(m_huart, &(rxBuffer[rxCount]), 1);
}

void UARTManager::transmit(uint8_t* buffer, uint16_t size)
{
	m_txBusy = true;
	if (m_halfDuplex)
		HAL_HalfDuplex_EnableTransmitter(m_huart);
	HAL_UART_Transmit_IT(m_huart, buffer, size);
}

void UARTManager::transmitSync(uint8_t* buffer, uint16_t size, uint32_t timeout)
{
	m_txBusy = true;
	if (m_halfDuplex)
		HAL_HalfDuplex_EnableTransmitter(m_huart);
	HAL_UART_Transmit(m_huart, buffer, size, timeout);
	if (m_halfDuplex)
	{
		HAL_HalfDuplex_EnableReceiver(m_huart);
		HAL_UART_Receive_IT(m_huart, &(rxBuffer[rxCount]), 1);
	}
	m_txBusy = false;
}

bool UARTManager::txBusy()
{
	return m_txBusy;
}

bool UARTManager::rxBusy()
{
	return m_rxBusy;
}

void UARTManager::txDoneISR()
{
	m_txBusy = false;
	if (m_txCallback)
		m_txCallback();

	if (m_halfDuplex)
	{
		HAL_HalfDuplex_EnableReceiver(m_huart);
		HAL_UART_Receive_IT(m_huart, &(rxBuffer[rxCount]), 1);
	}
}

void UARTManager::rxDoneISR(uint8_t* buffer, uint16_t size)
{
	UNUSED_ARG(buffer);
	UNUSED_ARG(size);
	rxCount++;
	if (m_stopCharEnabled && rxBuffer[rxCount-1] == m_stopChar)
	{
		if (m_rxCallback)
			m_rxCallback(rxBuffer, rxCount);
		rxCount = 0;
	} else if (rxCount == rxBufferMaxSize || rxCount == m_blockSize)
	{
		if (m_rxCallback)
			m_rxCallback(rxBuffer, rxCount);
		rxCount = 0;
	}

	if (m_halfDuplex)
		HAL_HalfDuplex_EnableReceiver(m_huart);
	HAL_UART_Receive_IT(m_huart, &(rxBuffer[rxCount]), 1);
}

extern "C"
{
	void HAL_UART_RxCpltCallback(UART_HandleTypeDef *huart)
	{
		UARTManager *mgr = uartsPool.getByHandle(huart);
		if (mgr)
			mgr->rxDoneISR(huart->pRxBuffPtr, huart->RxXferSize);

	}

	void HAL_UART_TxCpltCallback(UART_HandleTypeDef *huart)
	{
		UARTManager *mgr = uartsPool.getByHandle(huart);
		if (mgr)
			mgr->txDoneISR();

	}
}

///////////////////
// UARTSPool
IUARTManager* UARTSPool::get(uint8_t portNumber)
{
	if (m_uarts[portNumber] == nullptr)
	{
		m_uarts[portNumber] = new UARTManager(portNumber);
	}
	return m_uarts[portNumber];
}

UARTManager* UARTSPool::getByHandle(UART_HandleTypeDef* handle)
{
	if (handle == &huart1)
		return m_uarts[IUARTSPool::UART1];
	if (handle == &huart2)
		return m_uarts[IUARTSPool::UART2];
	if (handle == &huart3)
		return m_uarts[IUARTSPool::UART3];
	return nullptr;
}
