DAlexis/caustic-lasertag-system/cpp-sources/universal-device/high-level/src/bluetooth-bridge/hc05-configurator.cpp

/*
*    Copyright (C) 2016 by Aleksey Bulatov
*
*    This file is part of Caustic Lasertag System project.
*
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
*    @license GPL-3.0+ <http://spdx.org/licenses/GPL-3.0+>
*/

#include "bluetooth-bridge/hc05-configurator.hpp"
#include "hal/system-clock.hpp"
#include "core/logging.hpp"
#include <string.h>

HC05Configurator::HC05Configurator(DeviceName& deviceName, uint16_t& bluetoothPin) :
	m_devName(deviceName),
	m_pin(bluetoothPin)
{
}

void HC05Configurator::init(IIOPin* key, IUARTManager* uart)
{
	m_key = key;
	m_key->switchToOutput();
	m_uart = uart;
	m_uart->enableStopChar(true);
	m_uart->setStopChar('\n');
	m_uart->setBlockSize(100);
	m_uart->setRXDoneCallback([this](uint8_t* data, uint16_t size) { rxCallbackResult(data, size); });
}

void HC05Configurator::enterAT()
{
	m_key->set();
	systemClock->wait_us(10000);
}

void HC05Configurator::leaveAT()
{
	m_key->reset();
}

void HC05Configurator::waitForResult()
{
	Time time = systemClock->getTime();
	while (m_result == HC05Result::waiting)
	{
		if (systemClock->getTime() - time > 100000)
		{
			m_result = HC05Result::timeout;
			break;
		}
	}
}

void HC05Configurator::sendATCommand(const char* command, uint16_t size)
{
	m_result = HC05Result::waiting;
	m_response[0] = '\0';
	m_uart->transmitSync((uint8_t*) command, size);
}

HC05Configurator::HC05Result HC05Configurator::test()
{
	enterAT();
	systemClock->wait_us(100);
	const char* at="AT\r\n";
	sendATCommand(at, sizeof(at));
	waitForResult();
	return m_result;
}

HC05Configurator::HC05Result HC05Configurator::selectSpeed()
{
	// Trying default:
	m_uart->init(uartDefaultSpeed);
	HC05Result result = test();
	result = test();
	if (result == HC05Result::ok)
	{
	    debug << "HC-05 speed determined as " << uartDefaultSpeed << " b/s";
	} else {
		debug << "Default HC-05 speed rejected due to error while testing: " << parseResult(result);
		m_uart->init(uartTargetSpeed);
		result = test();
		result = test();
		if (result != HC05Result::ok)
		{
			error << "Cannot determine usart speed for HC-05!";
		} else {
		    debug << "HC-05 speed determined as " << uartTargetSpeed << " b/s";
		}
	}

	return result;
}

void HC05Configurator::configure()
{
	enterAT();

	char atName[35]="AT+NAME=";
	strcat(atName, m_devName.name);
	strcat(atName, "\r\n");

	const char* atUart="AT+UART=115200,1,0\r\n";

	char atPswd[35]="AT+PSWD=";
	char pass[5]="1234";
	pass[0] = m_pin / 1000 % 10 + '0';
	pass[1] = m_pin / 100 % 10  + '0';
	pass[2] = m_pin / 10 % 10   + '0';
	pass[3] = m_pin / 1 % 10    + '0';
	strcat(atPswd, pass);
	strcat(atPswd, "\r\n");

	systemClock->wait_us(10000);
	sendATCommand(atUart, strlen(atUart));
	waitForResult();
	if (m_result != HC05Result::ok)
	{
		error << "Cannot set UART speed for module: " << parseResult(m_result) << " resp: " << m_response;
		//return;
	} else {
		info << "UART Speed set properly!";
	}
	systemClock->wait_us(10000);
	sendATCommand(atName, strlen(atName));
	waitForResult();
	if (m_result != HC05Result::ok)
	{
		error << "Cannot set name for module: " << parseResult(m_result) << " resp: " << m_response;
		//return;
	} else {
		info << "Name set properly!";
	}

	systemClock->wait_us(10000);
	sendATCommand(atPswd, strlen(atPswd));
	waitForResult();
	if (m_result != HC05Result::ok)
	{
		error << "Cannot set password for module: " << parseResult(m_result) << " resp: " << m_response;
		//return;
	} else {
		info << "Password set properly!";
	}

	systemClock->wait_us(10000);
}

IUARTManager* HC05Configurator::getUART()
{
	return m_uart;
}

const char* HC05Configurator::parseResult(HC05Configurator::HC05Result result)
{
	switch(result)
	{
	case HC05Result::waiting: return "waiting";
	case HC05Result::failed: return "failed";
	case HC05Result::timeout: return "timeout";
	case HC05Result::ok: return "ok";
	case HC05Result::notRunned: return "notRunned";
	default: return "Invalid result";
	}
}

void HC05Configurator::rxCallbackResult(uint8_t* data, uint16_t size)
{
	memcpy(m_response, data, size);
	m_response[size] = '\0';
	if (size >= 2 && data[0] == 'O' && data[1] == 'K')
	{
		m_result = HC05Result::ok;
	} else {
		m_result = HC05Result::failed;
	}
}


bool HC05Configurator::quickTestBluetooth(IIOPin* key, IUARTManager* uart)
{
    UintParameter pinStub = 1234;
    DeviceName devNameStub;
    HC05Configurator* btConfigurator = new HC05Configurator(devNameStub, pinStub);
    btConfigurator->init(key, uart);
    bool result = (btConfigurator->selectSpeed() == HC05Result::ok);
    delete btConfigurator;
    return result;
}
