DAlexis/caustic-lasertag-system/cpp-sources/universal-device/low-level/Drivers/sd-stdperiph/sdcard-low-level.c

/*
 * sdcard-low-level.cpp
 *
 *  Created on: 08 янв. 2015 г.
 *      Author: alexey
 */

#ifdef USE_STDPERIPH_SDCARD

#include "sdcard-low-level.h"
#include "sdcard.h" // For SD_ProcessIRQSrc();
#include "stm32f10x.h"

/**
  * @brief  DeInitializes the SDIO interface.
  * @param  None
  * @retval None
  */
void SD_LowLevel_DeInit(void)
{
  GPIO_InitTypeDef  GPIO_InitStructure;

  /*!< Disable SDIO Clock */
  SDIO_ClockCmd(DISABLE);

  /*!< Set Power State to OFF */
  SDIO_SetPowerState(SDIO_PowerState_OFF);

  /*!< DeInitializes the SDIO peripheral */
  SDIO_DeInit();

  /*!< Disable the SDIO AHB Clock */
  RCC_AHBPeriphClockCmd(RCC_AHBPeriph_SDIO, DISABLE);

  /*!< Configure PC.08, PC.09, PC.10, PC.11, PC.12 pin: D0, D1, D2, D3, CLK pin */
  GPIO_InitStructure.GPIO_Pin = GPIO_Pin_8 | GPIO_Pin_9 | GPIO_Pin_10 | GPIO_Pin_11 | GPIO_Pin_12;
  GPIO_InitStructure.GPIO_Mode = GPIO_Mode_IN_FLOATING;
  GPIO_Init(GPIOC, &GPIO_InitStructure);

  /*!< Configure PD.02 CMD line */
  GPIO_InitStructure.GPIO_Pin = GPIO_Pin_2;
  GPIO_Init(GPIOD, &GPIO_InitStructure);
}

/**
  * @brief  Initializes the SD Card and put it into StandBy State (Ready for
  *         data transfer).
  * @param  None
  * @retval None
  */
void SD_LowLevel_Init(void)
{
  GPIO_InitTypeDef  GPIO_InitStructure;

  /*!< GPIOC and GPIOD Periph clock enable */
  RCC_APB2PeriphClockCmd(RCC_APB2Periph_GPIOC | RCC_APB2Periph_GPIOD/* | SD_DETECT_GPIO_CLK*/, ENABLE);

  /*!< Configure PC.08, PC.09, PC.10, PC.11, PC.12 pin: D0, D1, D2, D3, CLK pin */
  GPIO_InitStructure.GPIO_Pin = GPIO_Pin_8 | GPIO_Pin_9 | GPIO_Pin_10 | GPIO_Pin_11 | GPIO_Pin_12;
  GPIO_InitStructure.GPIO_Speed = GPIO_Speed_50MHz;
  GPIO_InitStructure.GPIO_Mode = GPIO_Mode_AF_PP;
  GPIO_Init(GPIOC, &GPIO_InitStructure);

  /*!< Configure PD.02 CMD line */
  GPIO_InitStructure.GPIO_Pin = GPIO_Pin_2;
  GPIO_Init(GPIOD, &GPIO_InitStructure);

  /*!< Configure SD_SPI_DETECT_PIN pin: SD Card detect pin */
  /*
  GPIO_InitStructure.GPIO_Pin = SD_DETECT_PIN;
  GPIO_InitStructure.GPIO_Mode = GPIO_Mode_IPU;
  GPIO_Init(SD_DETECT_GPIO_PORT, &GPIO_InitStructure);
  */

  /*!< Enable the SDIO AHB Clock */
  RCC_AHBPeriphClockCmd(RCC_AHBPeriph_SDIO, ENABLE);

  /*!< Enable the DMA2 Clock */
  RCC_AHBPeriphClockCmd(RCC_AHBPeriph_DMA2, ENABLE);
}

/**
  * @brief  Configures the DMA2 Channel4 for SDIO Tx request.
  * @param  BufferSRC: pointer to the source buffer
  * @param  BufferSize: buffer size
  * @retval None
  */
void SD_LowLevel_DMA_TxConfig(uint32_t *BufferSRC, uint32_t BufferSize)
{

  DMA_InitTypeDef DMA_InitStructure;

  DMA_ClearFlag(DMA2_FLAG_TC4 | DMA2_FLAG_TE4 | DMA2_FLAG_HT4 | DMA2_FLAG_GL4);

  /*!< DMA2 Channel4 disable */
  DMA_Cmd(DMA2_Channel4, DISABLE);

  /*!< DMA2 Channel4 Config */
  DMA_InitStructure.DMA_PeripheralBaseAddr = (uint32_t)SDIO_FIFO_ADDRESS;
  DMA_InitStructure.DMA_MemoryBaseAddr = (uint32_t)BufferSRC;
  DMA_InitStructure.DMA_DIR = DMA_DIR_PeripheralDST;
  DMA_InitStructure.DMA_BufferSize = BufferSize / 4;
  DMA_InitStructure.DMA_PeripheralInc = DMA_PeripheralInc_Disable;
  DMA_InitStructure.DMA_MemoryInc = DMA_MemoryInc_Enable;
  DMA_InitStructure.DMA_PeripheralDataSize = DMA_PeripheralDataSize_Word;
  DMA_InitStructure.DMA_MemoryDataSize = DMA_MemoryDataSize_Word;

  DMA_InitStructure.DMA_Mode = DMA_Mode_Normal;
  DMA_InitStructure.DMA_Priority = DMA_Priority_High;
  DMA_InitStructure.DMA_M2M = DMA_M2M_Disable;
  DMA_Init(DMA2_Channel4, &DMA_InitStructure);

  /*!< DMA2 Channel4 enable */
  DMA_Cmd(DMA2_Channel4, ENABLE);
}
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
